CamMorelli/hshs-project-FirstStageTest/docs/teensy-4.0/dimensions_teensy40.png

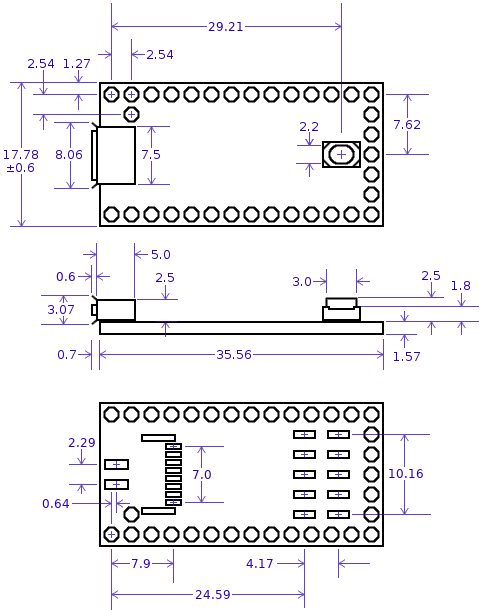
docs/teensy-4.0/dimensions_teensy40.png
