CamMorelli/hshs-project-FirstStageTest/Hardware/HSHS Interface Board 0110B/Assembly Documents/HSHS Interface Board 0110B.xlsx

Reference | Value | DESCRIPTION | Qty
C1-C4 | 1µF | CAP CER 1UF 25V X5R 0603 | 4
C5, C8 | 0.1µF |  | 2
C6, C9 | 33nF |  | 2
C7, C102, C104, C105, C202, C204, C205, C302, C304, C305, C402, C404, C405 | 10nF | CAP CER 10000PF 25V X7R 0603 | 13
C101, C201, C301, C401 | 10µF | CAP CER 10UF 16V X5R 0805 | 4
C103, C203, C303, C403 | 22µF | CAP CER 22UF 10V X7S 0805 | 4
D1-D3, D5 | LED Green | LED GREEN CLEAR 0603 SMD | 4
D4, D103, D203, D303, D403 | LED Blue | LED BLUE CLEAR 0603 SMD | 5
D101, D201, D301, D401 | LED Red | LED RED CLEAR 0603 SMD | 4
D102, D202, D302, D402 | LED Yellow | LED YELLOW CLEAR 0603 SMD | 4
H1-H4 | MountingHole |  | 4
IC1, IC2 | ACS725LLCTR-10AU-T |  | 2
J1 | Conn_01x02_Pin |  | 1
J2 | 5788801-1 | CONN D-SUB RCPT 25POS R/A SLDR | 1
J3 | 5788798-1 |  | 1
NT1 | NetTie_2 |  | 1
Q1, Q101, Q102, Q201, Q202, Q301, Q302, Q401, Q402 | SSM3K376R_A | MOSFET N-CH 30V 4A SOT23F | 9
R1, R3, R13, R105, R107, R205, R207, R305, R307, R405, R407 | 500 | RES 499 OHM 1% 1/10W 0603 | 11
R2, R4, R10, R11, R15 | 1k | -- mixed values -- | 5
R5, R102, R202, R302, R402 | 25k | -- mixed values -- | 5
R6-R9, R12, R104, R106, R204, R206, R304, R306, R404, R406 | 10k | RES 10K OHM 1% 1/10W 0603 | 13
R14 | 0.1 | RES 0.1 OHM 1% 1/3W 0805 | 1
R101, R103, R201, R203, R301, R303, R401, R403 | 15k | RES 15K OHM 1% 1/10W 0603 | 8
TP1-TP4, TP101, TP201, TP301, TP401 | 5015 | SMT Test Point- Micro Miniature-1000 pc Reels | 8
U1 | Teensy4.0_28_Pins | TEENSY 4.0 (HEADERS) | 1
U101, U201, U301, U401 | TPSM82902SISR | 3-V TO 17-V, 2-A HIGH EFFICIENCY | 4
VR101, VR201, VR301, VR401 | SM-42X104 | TRIMMER 100K OHM 0.25W GW TOP | 4
