CamMorelli/hshs-project-FirstStageTest/Hardware/HSHS Interface Board/Assembly Documents/HSHS Interface Board Symbol Table B.xlsx

Reference | Value | DESCRIPTION | Qty
C1-C5, C7 | 1¬µF | CAP CER 1UF 25V X5R 0603 | 6
C6, C9-C11, C14-C16, C19-C21, C24-C26 | 10nF | CAP CER 10000PF 25V X7R 0603 | 13
C8, C13, C18, C23 | 10¬µF | CAP CER 10UF 16V X5R 0805 | 4
C12, C17, C22, C27 | 22¬µF | CAP CER 22UF 10V X7S 0805 | 4
D1-D4 | LED Green | LED GREEN CLEAR 0603 SMD | 4
D5, D7, D10, D13, D16 | LED Blue | LED BLUE CLEAR 0603 SMD | 5
D6, D9, D12, D15 | LED Yellow | LED YELLOW CLEAR 0603 SMD | 4
D8, D11, D14, D17 | LED Red | LED RED CLEAR 0603 SMD | 4
J1 | Conn_01x02_Pin |  | 1
J2 | 2301845-2 | CONN D-SUB RCPT 15POS R/A SLDR | 1
J3 | 5788801-1 | CONN D-SUB RCPT 25POS R/A SLDR | 1
NT1 | NetTie_2 |  | 1
Q1-Q9 | SSM3K376R_A | MOSFET N-CH 30V 4A SOT23F | 9
R1, R3, R5, R7, R8, R10, R17, R18, R30, R31, R43, R44, R56, R57 | 500 | RES 499 OHM 1% 1/10W 0603 | 14
R2, R6 | 1k | RES 1K OHM 1% 1/10W 0603 | 2
R4, R9, R11-R15, R19-R22, R26, R27, R32-R35, R39, R40, R45-R48, R52, R53, R58-R61, R65, R66 | 10k | RES 10K OHM 1% 1/10W 0603 | 31
R16, R23, R24, R36, R37, R49, R50, R62, R63 | 0.1 | RES 0.1 OHM 1% 1/3W 0805 | 9
R25, R29, R38, R42, R51, R55, R64, R68 | 15k | RES 15K OHM 1% 1/10W 0603 | 8
R28, R41, R54, R67 | 25k | RES SMD 24.9K OHM 1% 1/10W 0603 | 4
TP1-TP13 | 5015 | SMT Test Point- Micro Miniature-1000 pc Reels | 13
U1 | Teensy4.0_28_Pins | TEENSY 4.0 (HEADERS) | 1
U2-U5 | TPSM82902SISR | 3-V TO 17-V, 2-A HIGH EFFICIENCY | 4
VR1-VR4 | SM-42X104 | TRIMMER 100K OHM 0.25W GW TOP | 4
