CamMorelli/hshs-project-FirstStageTest/docs/Off Board Components/Lasers/Nichia NDG7475.pdf

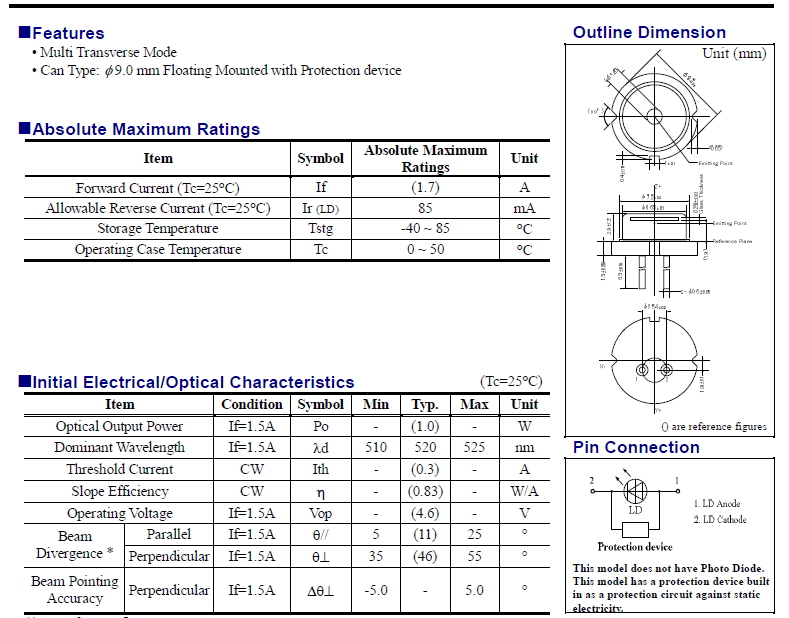
[picture p5: figure]
