CamMorelli/hshs-project-FirstStageTest/Hardware/HSHS Test Board 0111/HSHS Test Board 0111.csv

Reference | Value | Footprint | Datasheet | AVAILABILITY | Arrow Part Number | Arrow Price/Stock | DESCRIPTION | Digikey Price Stock | Digikey_Part_Number | Height | MF | MP | Manufacturer Part Number | Manufacturer_Name | Mouser Part Number | Mouser Price/Stock | PACKAGE | PRICE | PURCHASE-URL | Qty
J1 | DB25_Receptacle | Global_Footprint_Library:57888011_A | https://www.te.com/commerce/DocumentDelivery/DDEController?Action=showdoc |  | 5788801-1 | https://www.arrow.com/en/products/5788801-1/te-connectivity?region=nac | CONN D-SUB RCPT 25POS R/A SLDR | https://www.digikey.com/en/products/detail/te-connectivity-amp-connectors/5788801-1/1279852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 | A35139-ND | 12.93 |  |  | 5788801-1 | TE Connectivity | 571-5788801-1 | https://www.mouser.co.uk/ProductDetail/TE-Connectivity-AMP/5788801-1?qs=PmjM%2FwY1RToSHOZP%252ByStZg%3D%3D |  | 8.04 |  | 1
J2 | DB25_Plug | Global_Footprint_Library:5788794_1 Mod From 57888011_A | https://www.te.com/commerce/DocumentDelivery/DDEController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 |  |  |  | CONN D-SUB PLUG 25POS R/A SLDR | https://www.digikey.com/en/products/detail/te-connectivity-amp-connectors/5788794-1/1279845 | A35132-ND |  |  |  | 5788794-1 | TE Connectivity |  |  |  |  |  | 1
R1-R8 | 0.1 | Resistor_SMD:R_0805_2012Metric | ~ |  |  |  |  |  |  |  |  |  |  |  |  |  |  |  |  | 8
TP1-TP8 | 5015 | Global_Footprint_Library:KEYSTONE_5015 | https://www.keyelco.com/userAssets/file/M65p55.pdf | In Stock |  |  | SMT Test Point- Micro Miniature-1000 pc Reels | https://www.digikey.com/en/products/detail/keystone-electronics/5015/278885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 | 36-5015CT-ND |  | Keystone Electronics | 5015 | 5015 | Keystone Electronics |  |  | None | 0.3684 | https://pricing.snapeda.com/search/part/5015/?ref=eda | 8
