CamMorelli/hshs-project-FirstStageTest/Hardware/HSHS Test Board 0111/Assembly Docs/HSHS Test Board 0111.xlsx

Reference | Value | Qty
J1 | DB25_Receptacle | 1
J2 | DB25_Plug | 1
R1-R8 | 0.1 | 8
TP1-TP8 | 5015 | 8
