CamMorelli/hshs-project-FirstStageTest/Hardware/HSHS Interface Board 0110A/Assembly Documents/Screen Shot 2024-03-24 at 6.15.10 PM.png

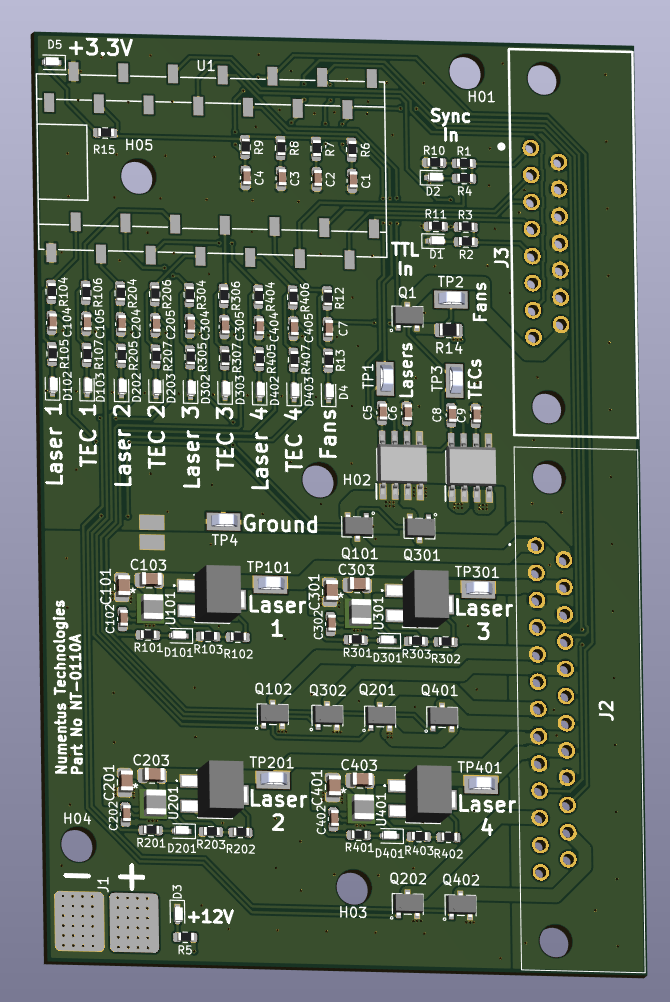
Hardware/HSHS Interface Board 0110A/Assembly Documents/Screen Shot 2024-03-24 at 6.15.10 PM.png
