CamMorelli/hshs-project-FirstStageTest/Hardware/HSHS Interface Board 0110B/Assembly Documents/Screen Shot 2024-04-10 at 11.27.31 AM.png

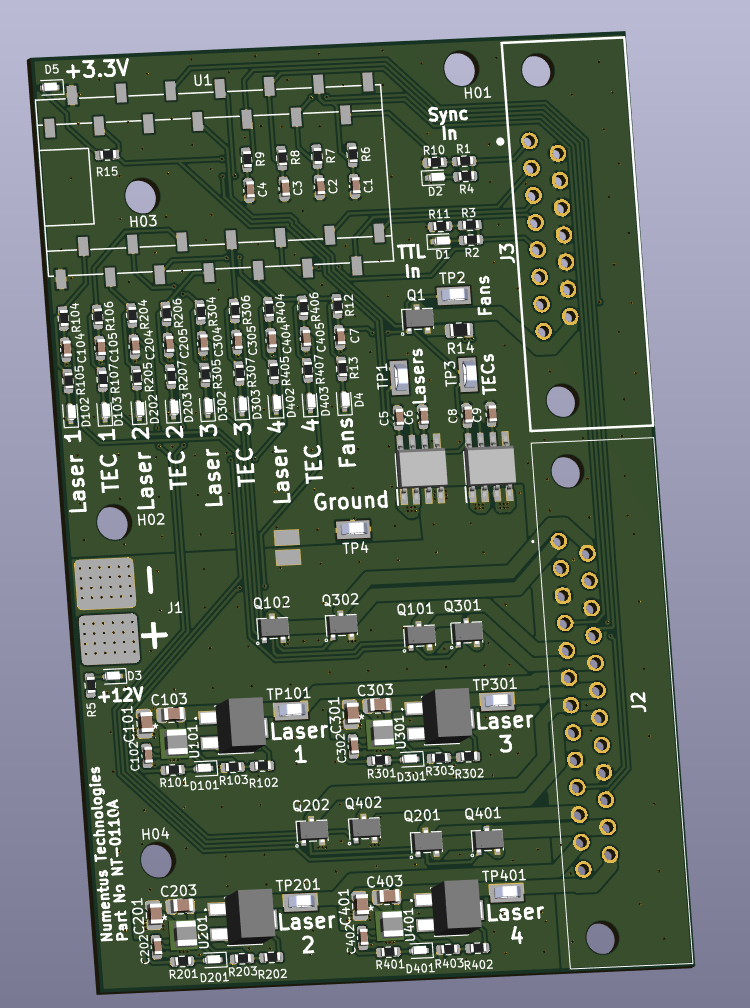
Hardware/HSHS Interface Board 0110B/Assembly Documents/Screen Shot 2024-04-10 at 11.27.31 AM.png
