CamMorelli/hshs-project-FirstStageTest/Hardware/HSHS Interface Board 1010C/Assembly Documents/Screen Shot 2024-04-26 at 10.37.50 AM.png

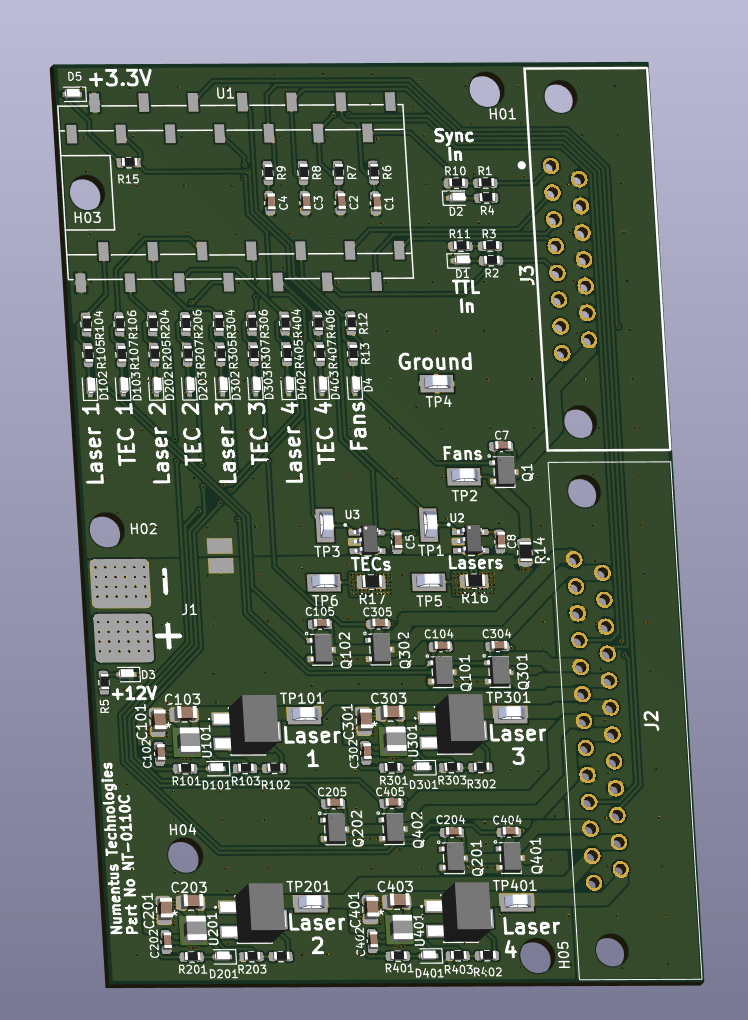
Hardware/HSHS Interface Board 1010C/Assembly Documents/Screen Shot 2024-04-26 at 10.37.50 AM.png
