CamMorelli/hshs-project-FirstStageTest/Hardware/HSHS Interface Board/Assembly Documents/Screen Shot 2024-03-11 at 11.47.38 AM.png

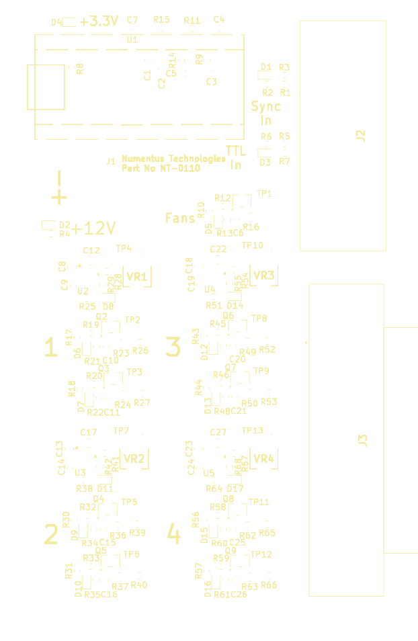
Hardware/HSHS Interface Board/Assembly Documents/Screen Shot 2024-03-11 at 11.47.38 AM.png
