CamMorelli/hshs-project-FirstStageTest/Hardware/HSHS Interface Board/Assembly Documents/Screen Shot 2024-03-11 at 12.02.20 PM.png

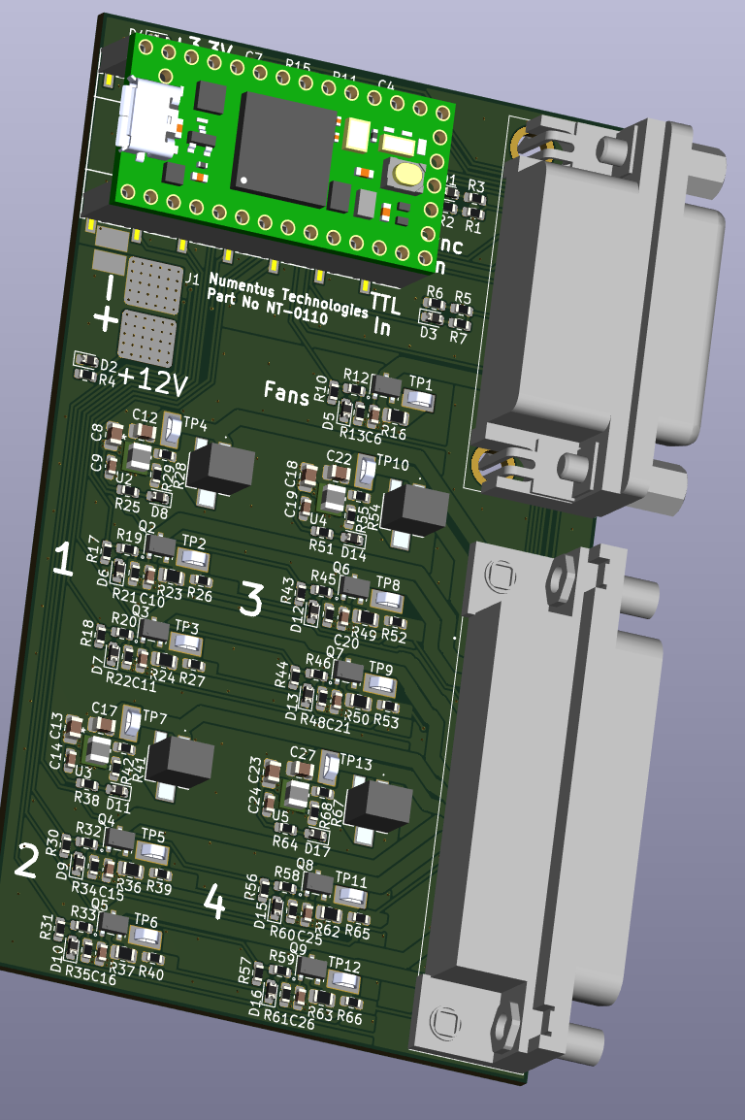
Hardware/HSHS Interface Board/Assembly Documents/Screen Shot 2024-03-11 at 12.02.20 PM.png
