CamMorelli/hshs-project-FirstStageTest/Hardware/HSHS Test Board 0111/Assembly Docs/Screen Shot 2024-04-04 at 2.46.10 PM.png

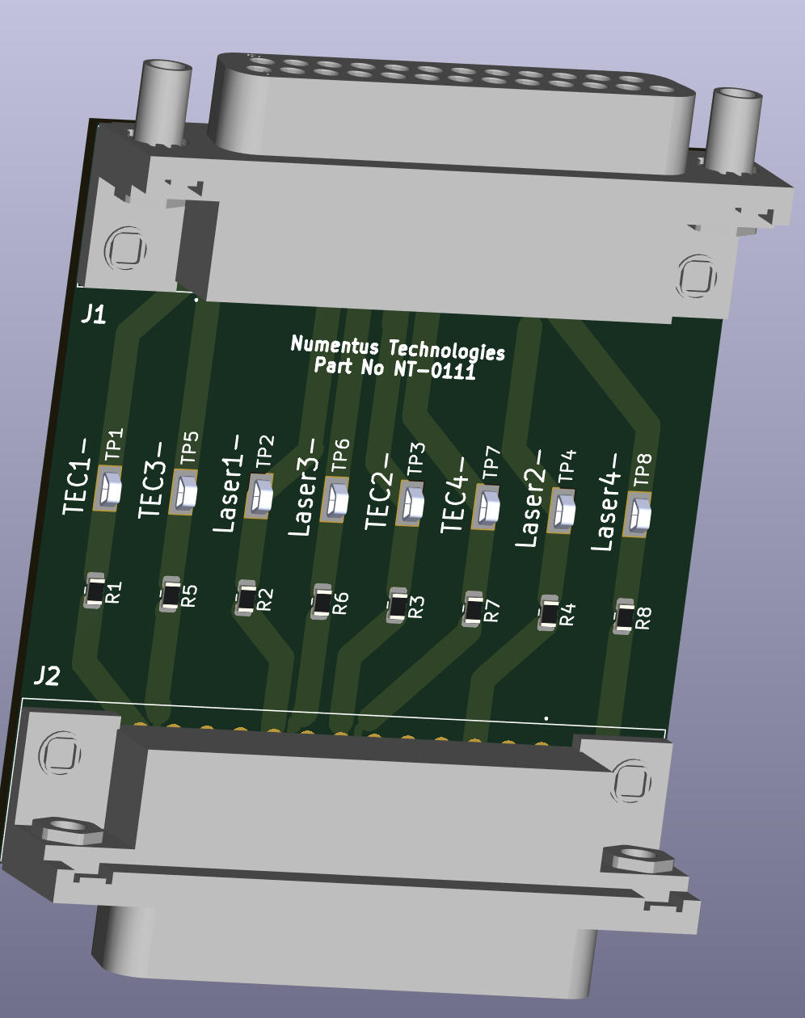
Hardware/HSHS Test Board 0111/Assembly Docs/Screen Shot 2024-04-04 at 2.46.10 PM.png
