CamMorelli/hshs-project-FirstStageTest/Hardware/HSHS Interface Board 1010C/Assembly Documents/HSHS Interface Board 1010C-F_Fab.pdf

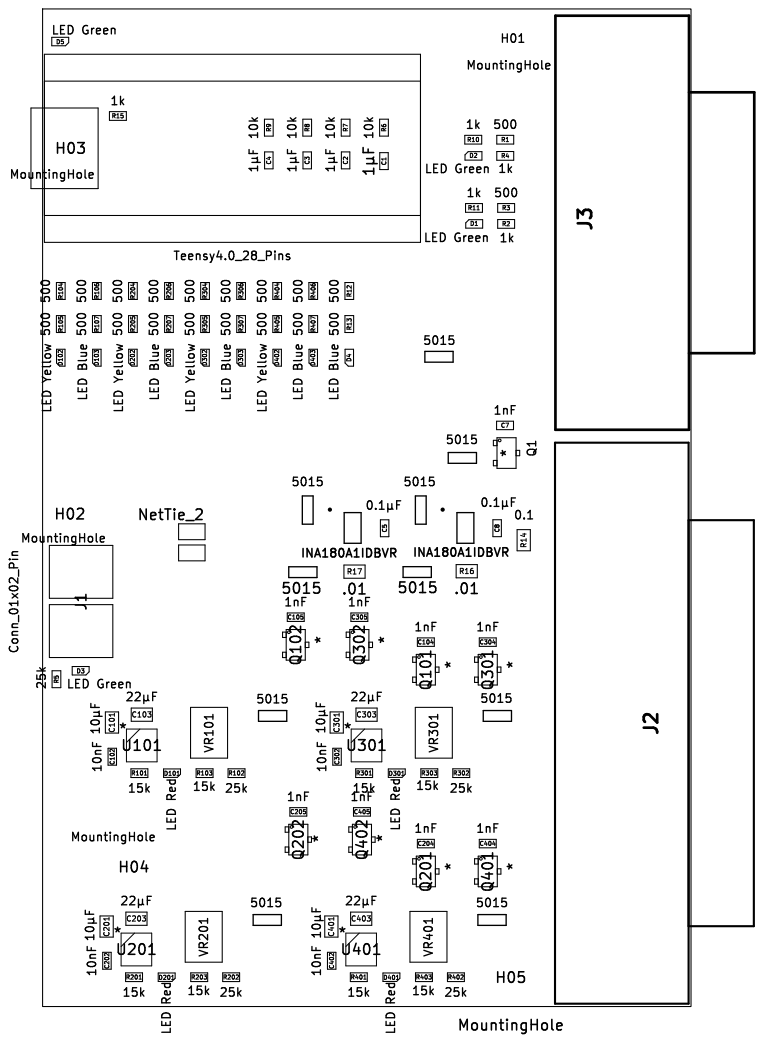
[picture p20: page 1]

* Q101 þÿ10µF C101 MountingHole H03 þÿ10µF C201 5015 MountingHole H05 10nF C402 *U201
