CamMorelli/hshs-project-FirstStageTest/Hardware/HSHS Test Board 0111/Assembly Docs/HSHS Test Board 0111-F_Silkscreen.pdf

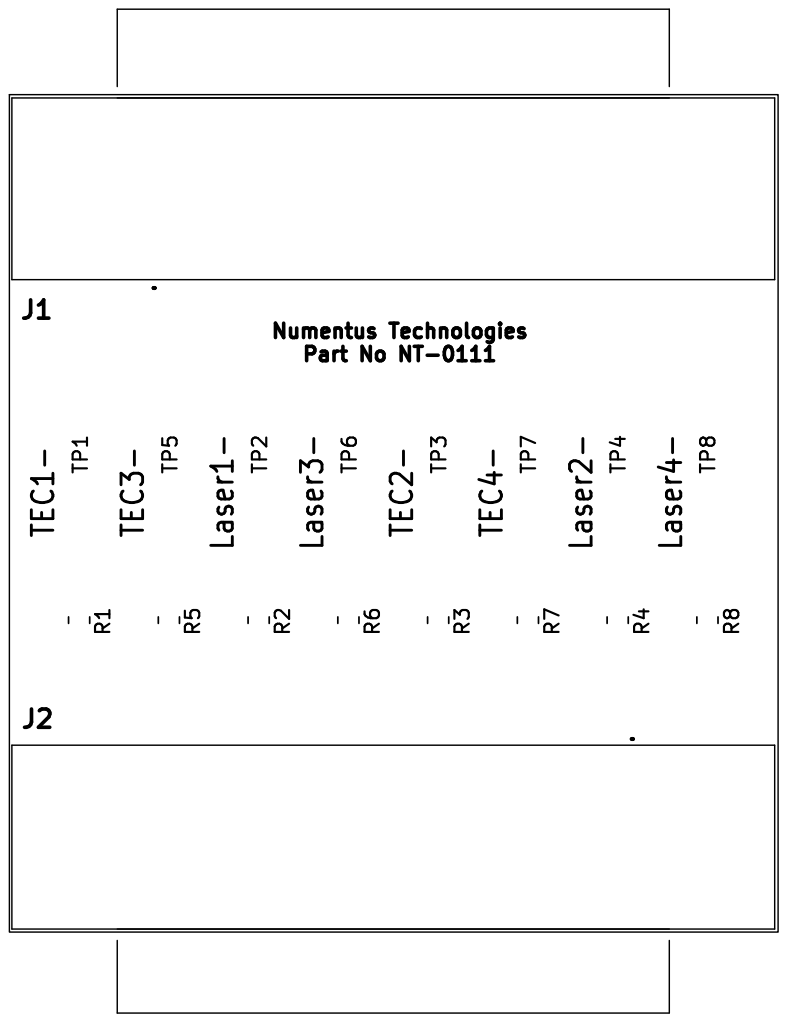
[picture p21: page 1]

TEC4- Laser1- Laser2- TEC1- TEC3- Laser3- Laser4- TEC2- Numentus Technologies Part No NT-0111 TP8 J1
