CamMorelli/hshs-project-FirstStageTest/docs/PCB Components/Connectors/ENG_CD_2301845_H.pdf

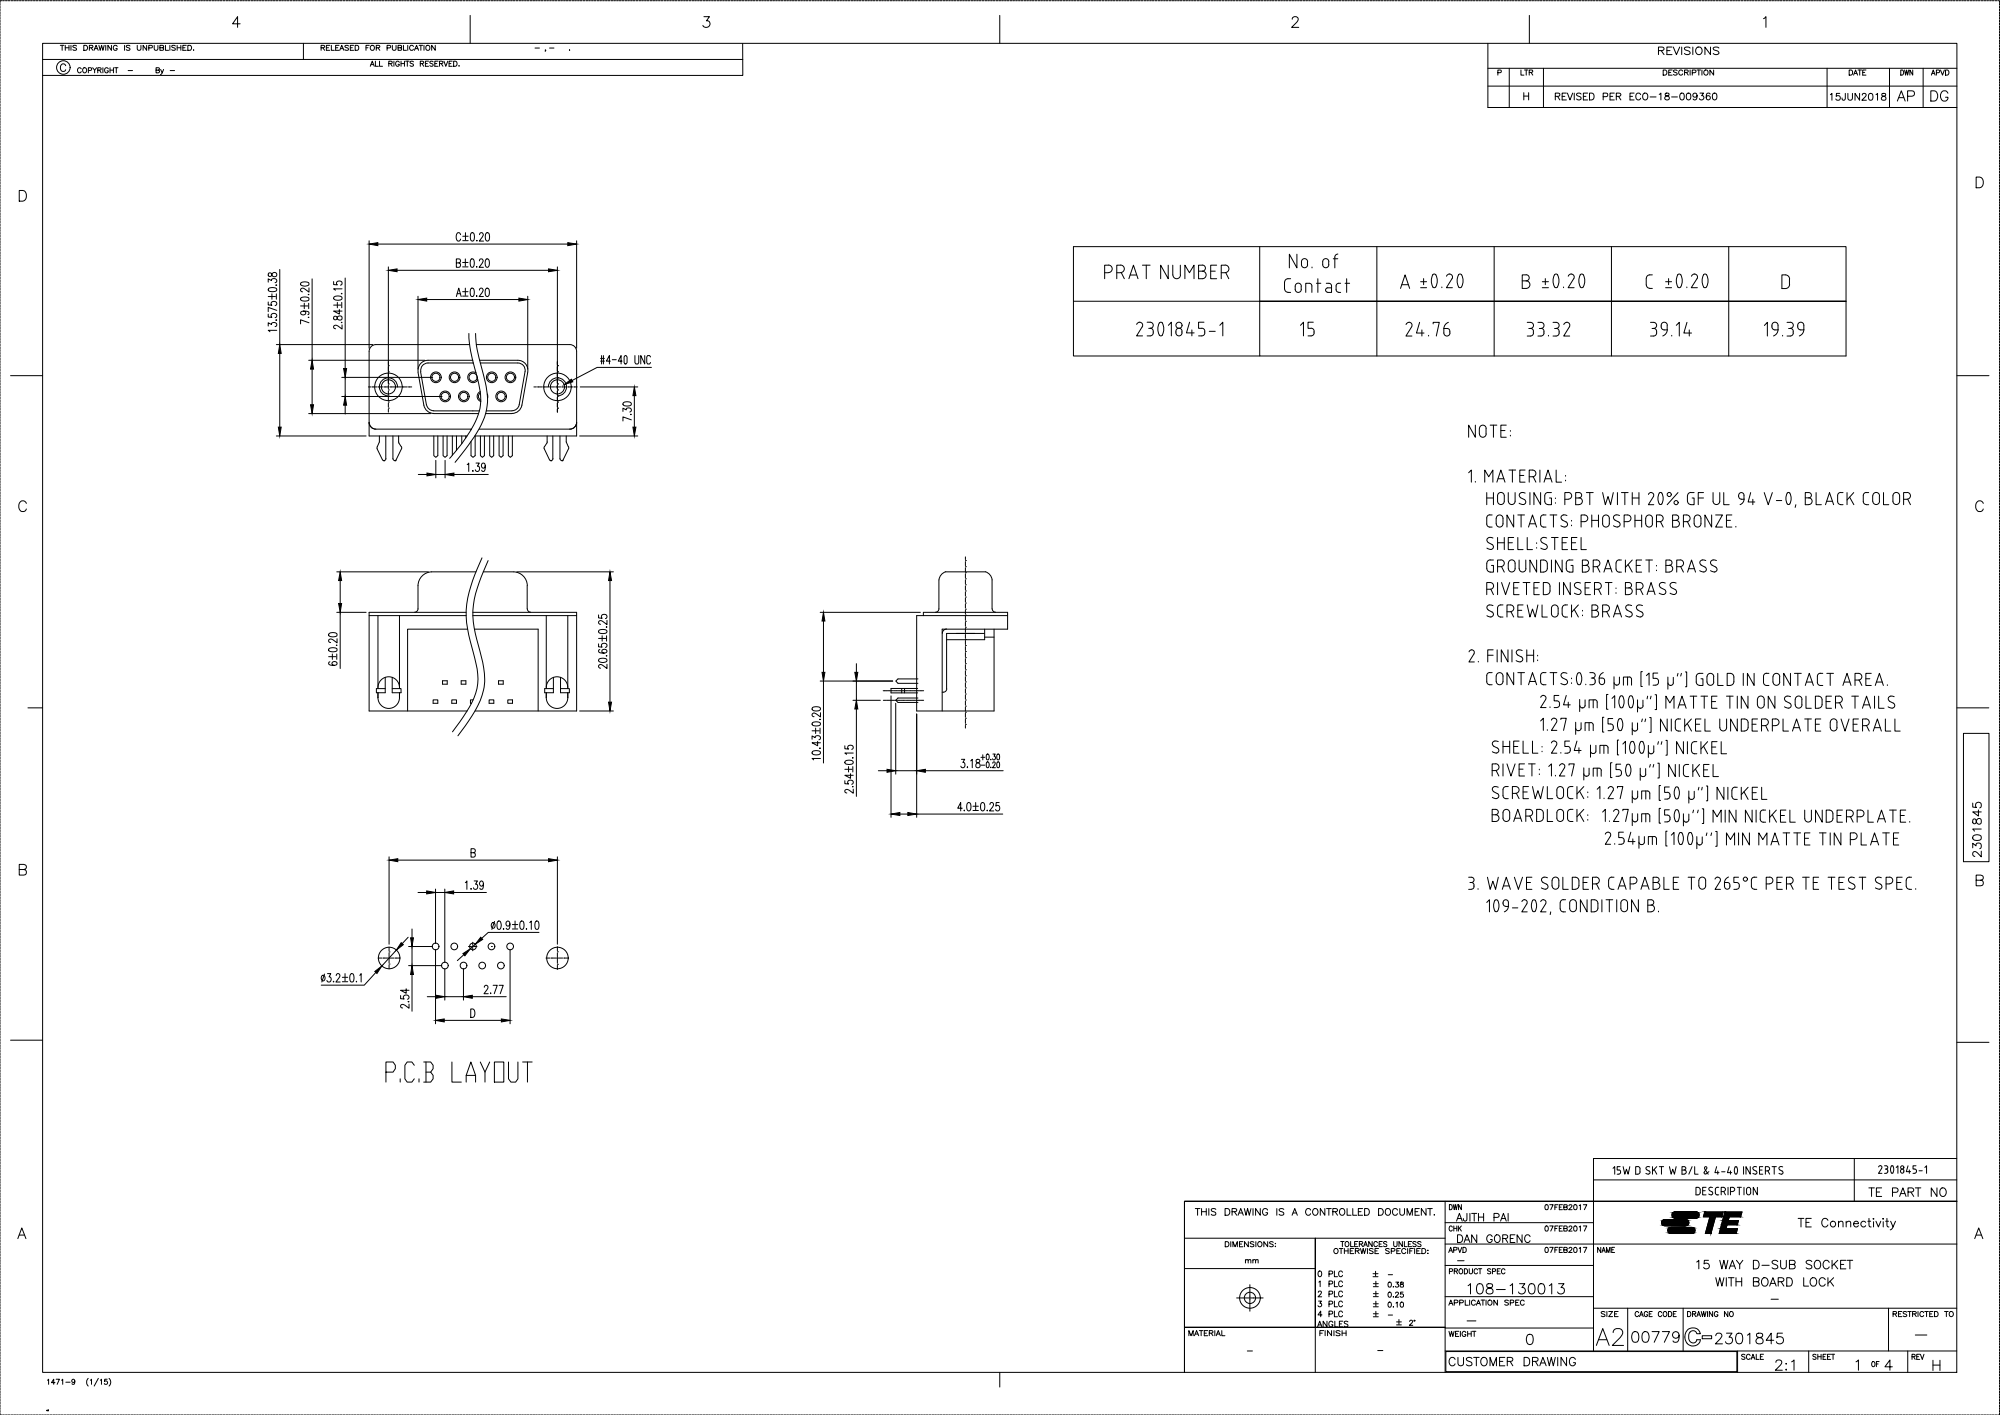
[picture p29: page 1]

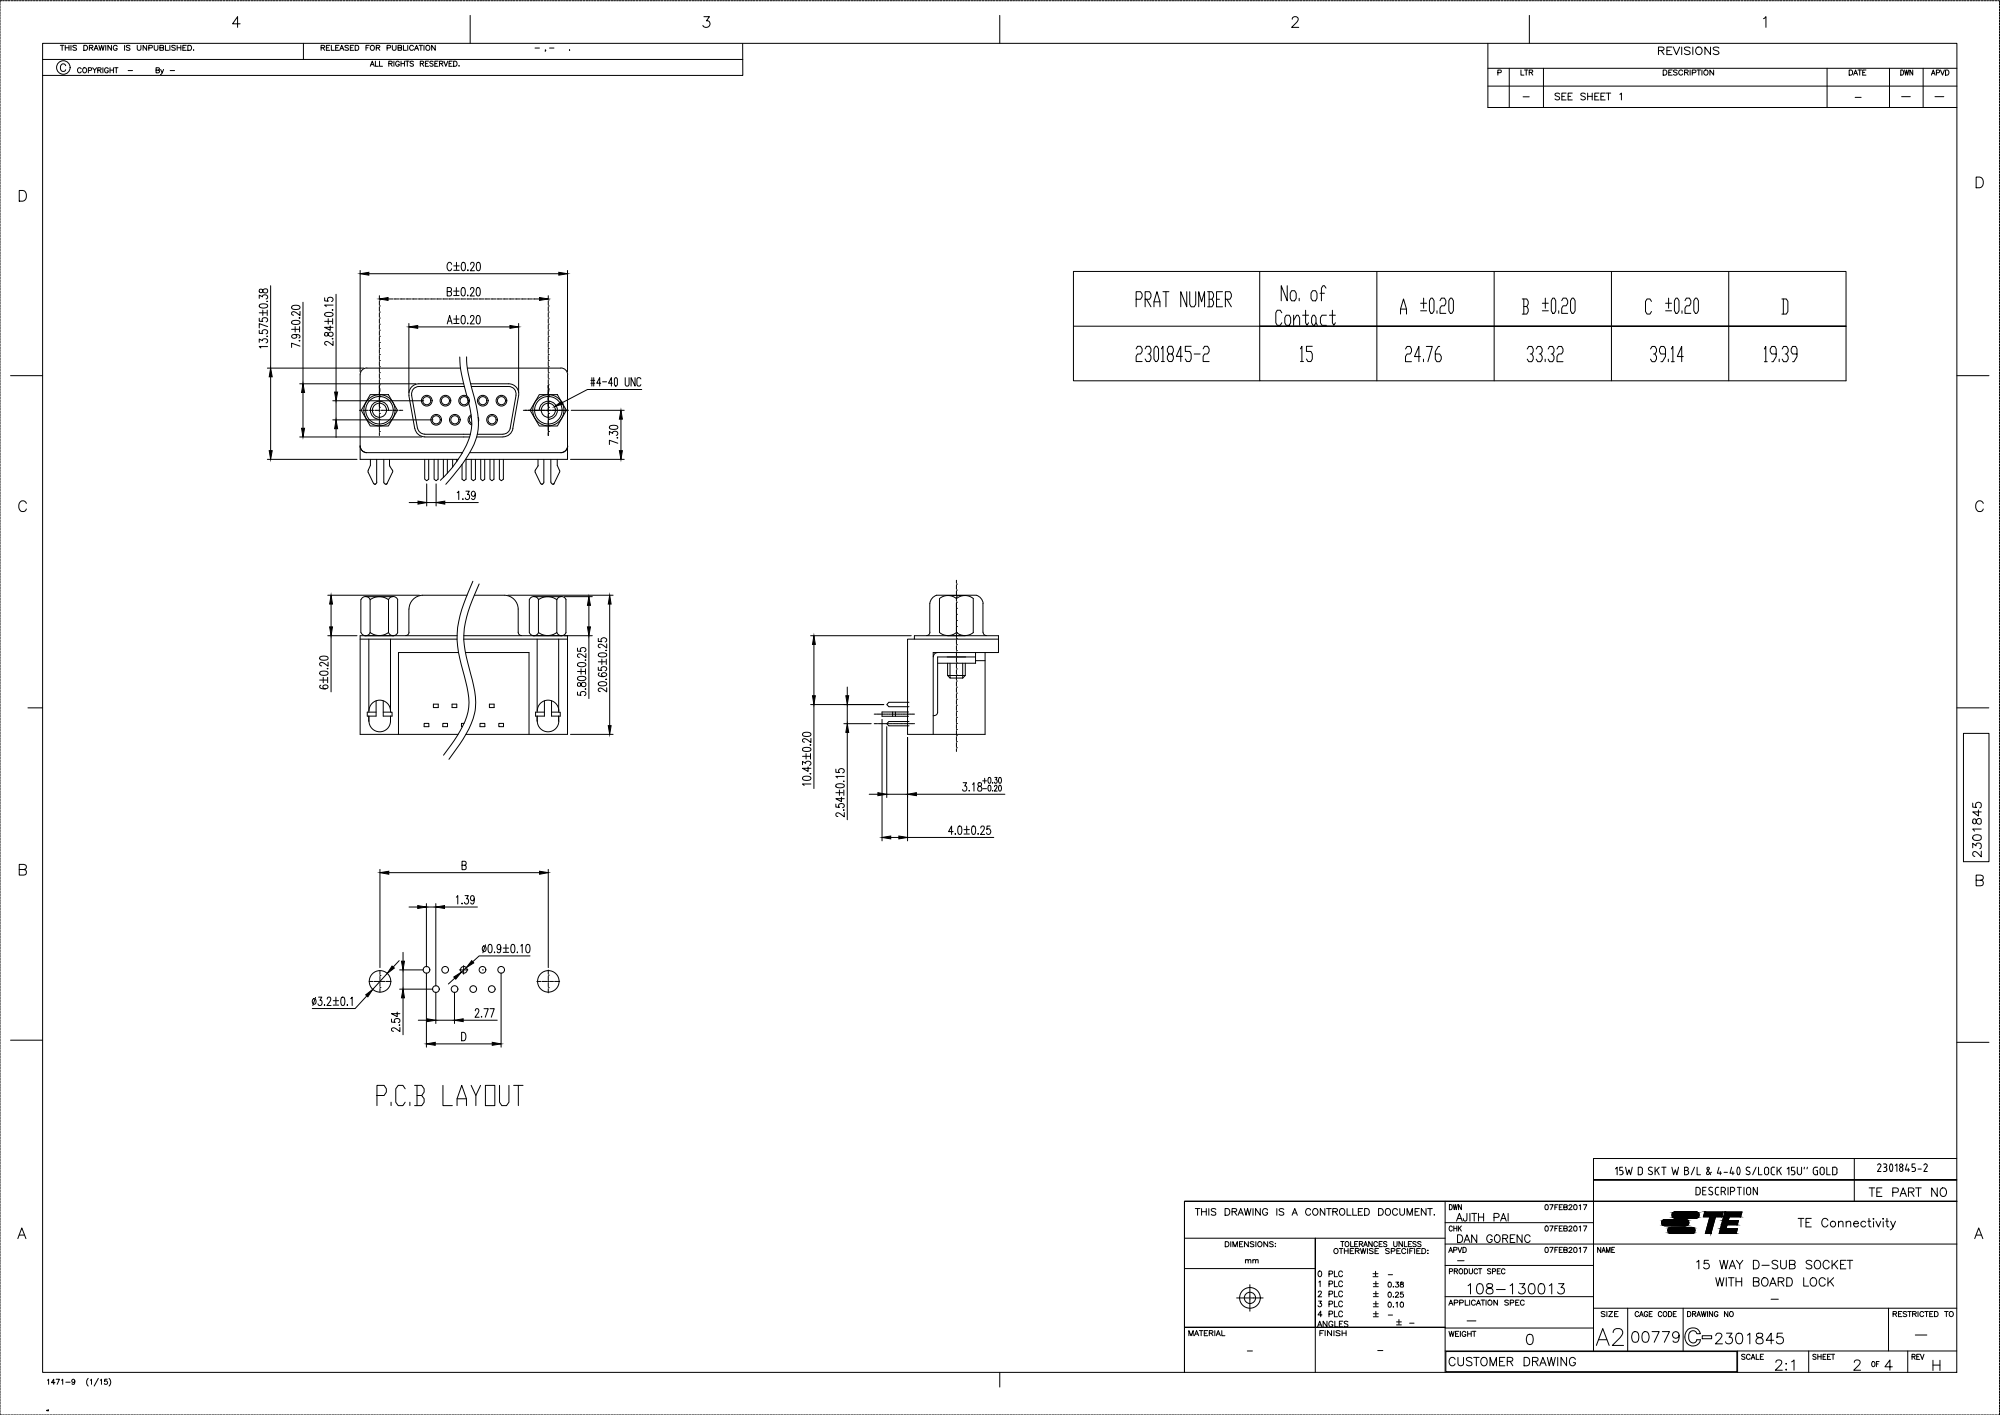
[picture p30: page 2]

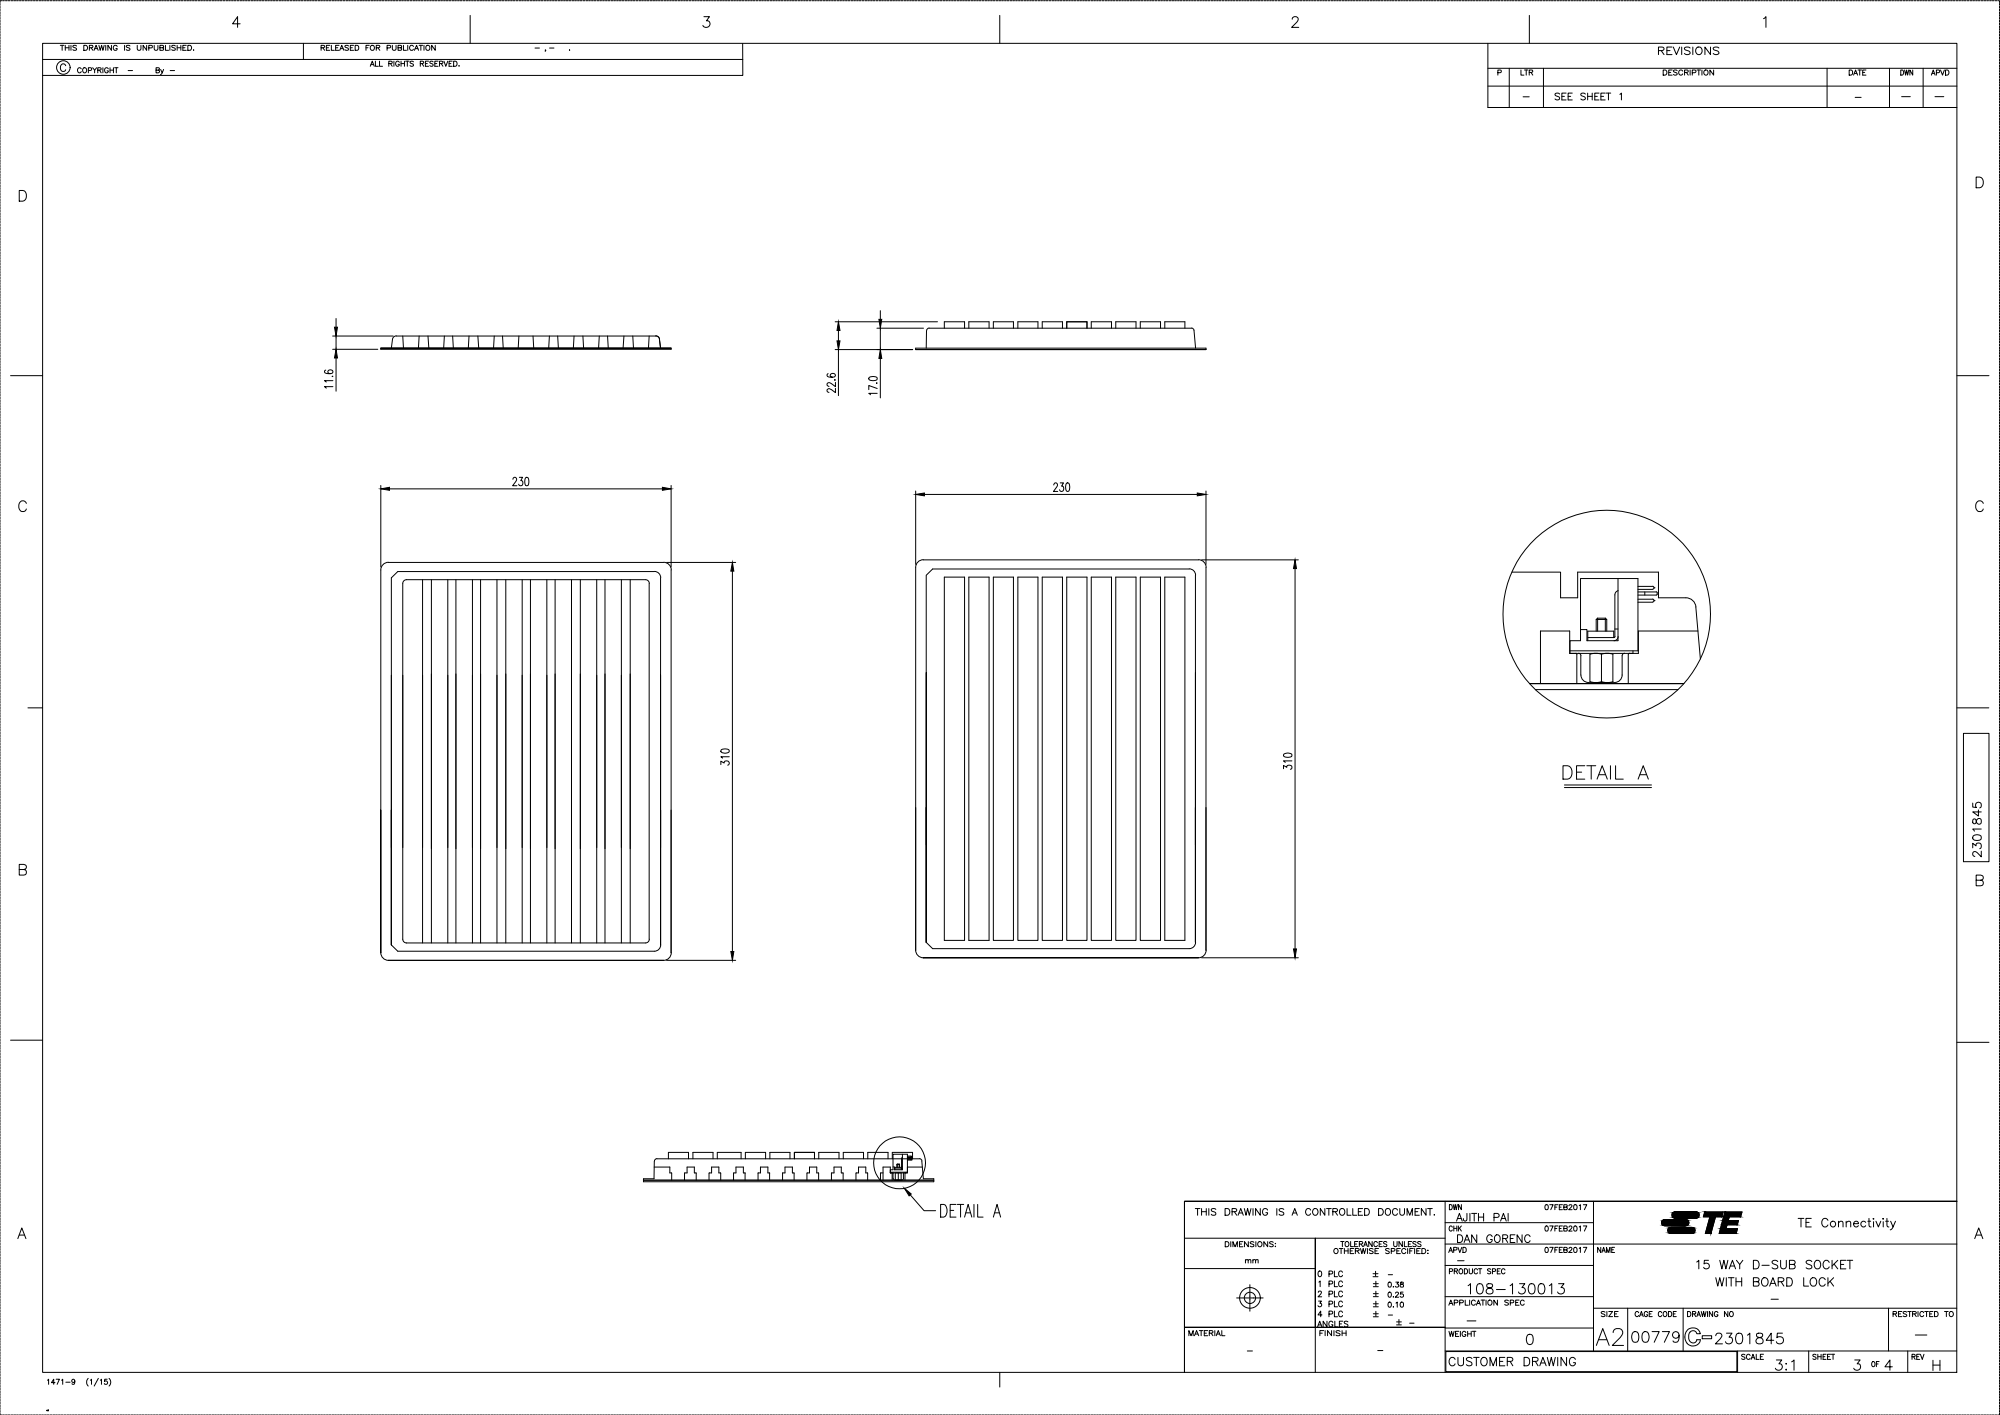
[picture p31: page 3]

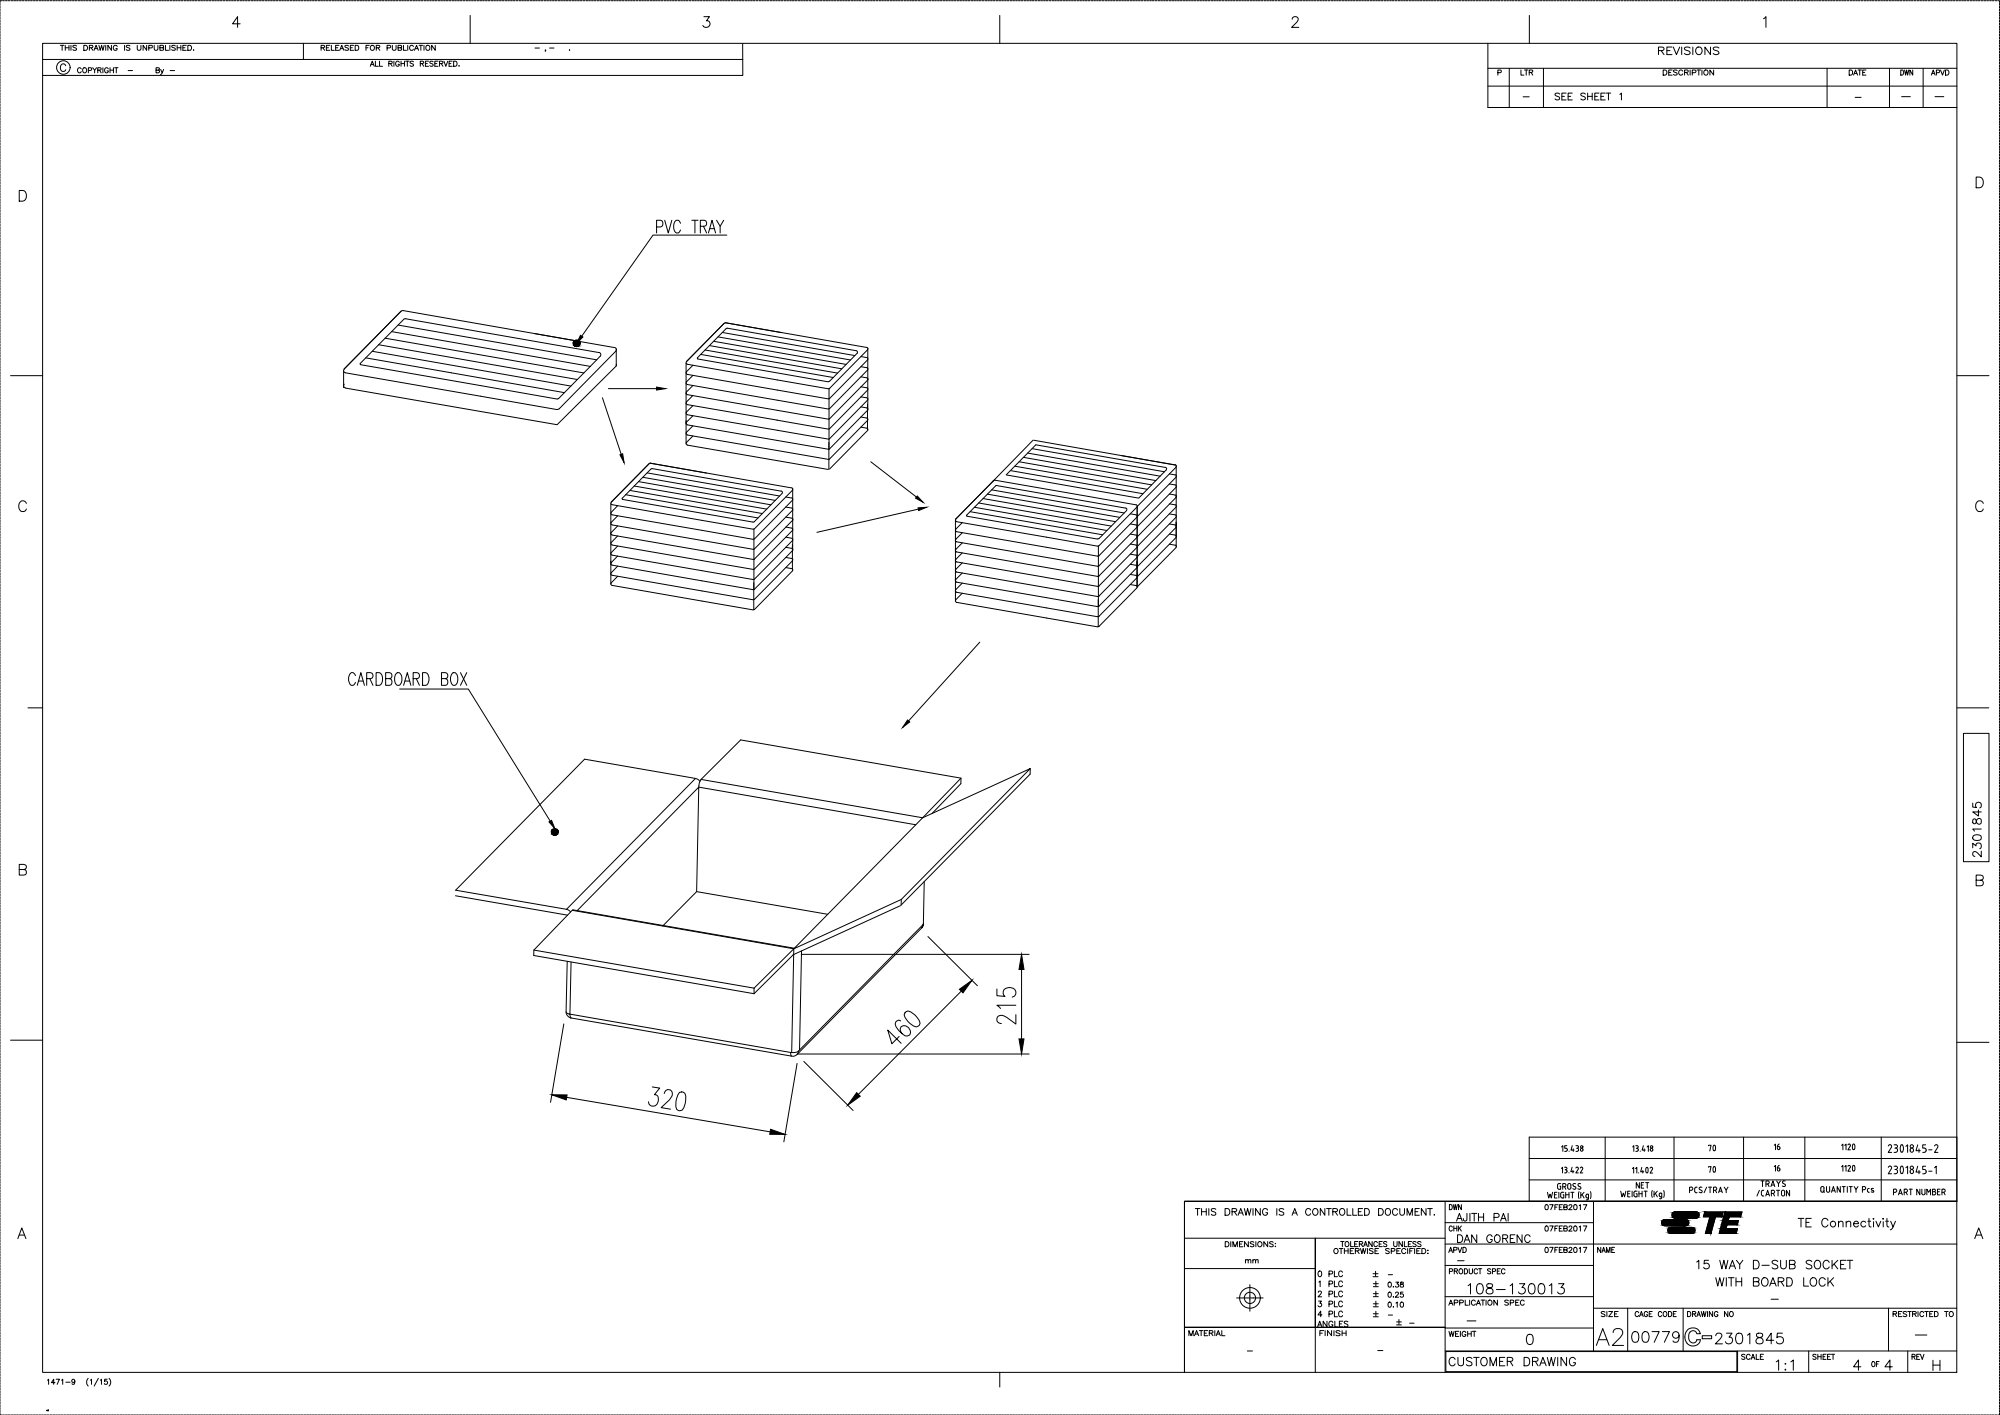
[picture p32: page 4]
