CamMorelli/hshs-project-FirstStageTest/docs/PCB Components/Connectors/ENG_CD_5788798_A1.pdf

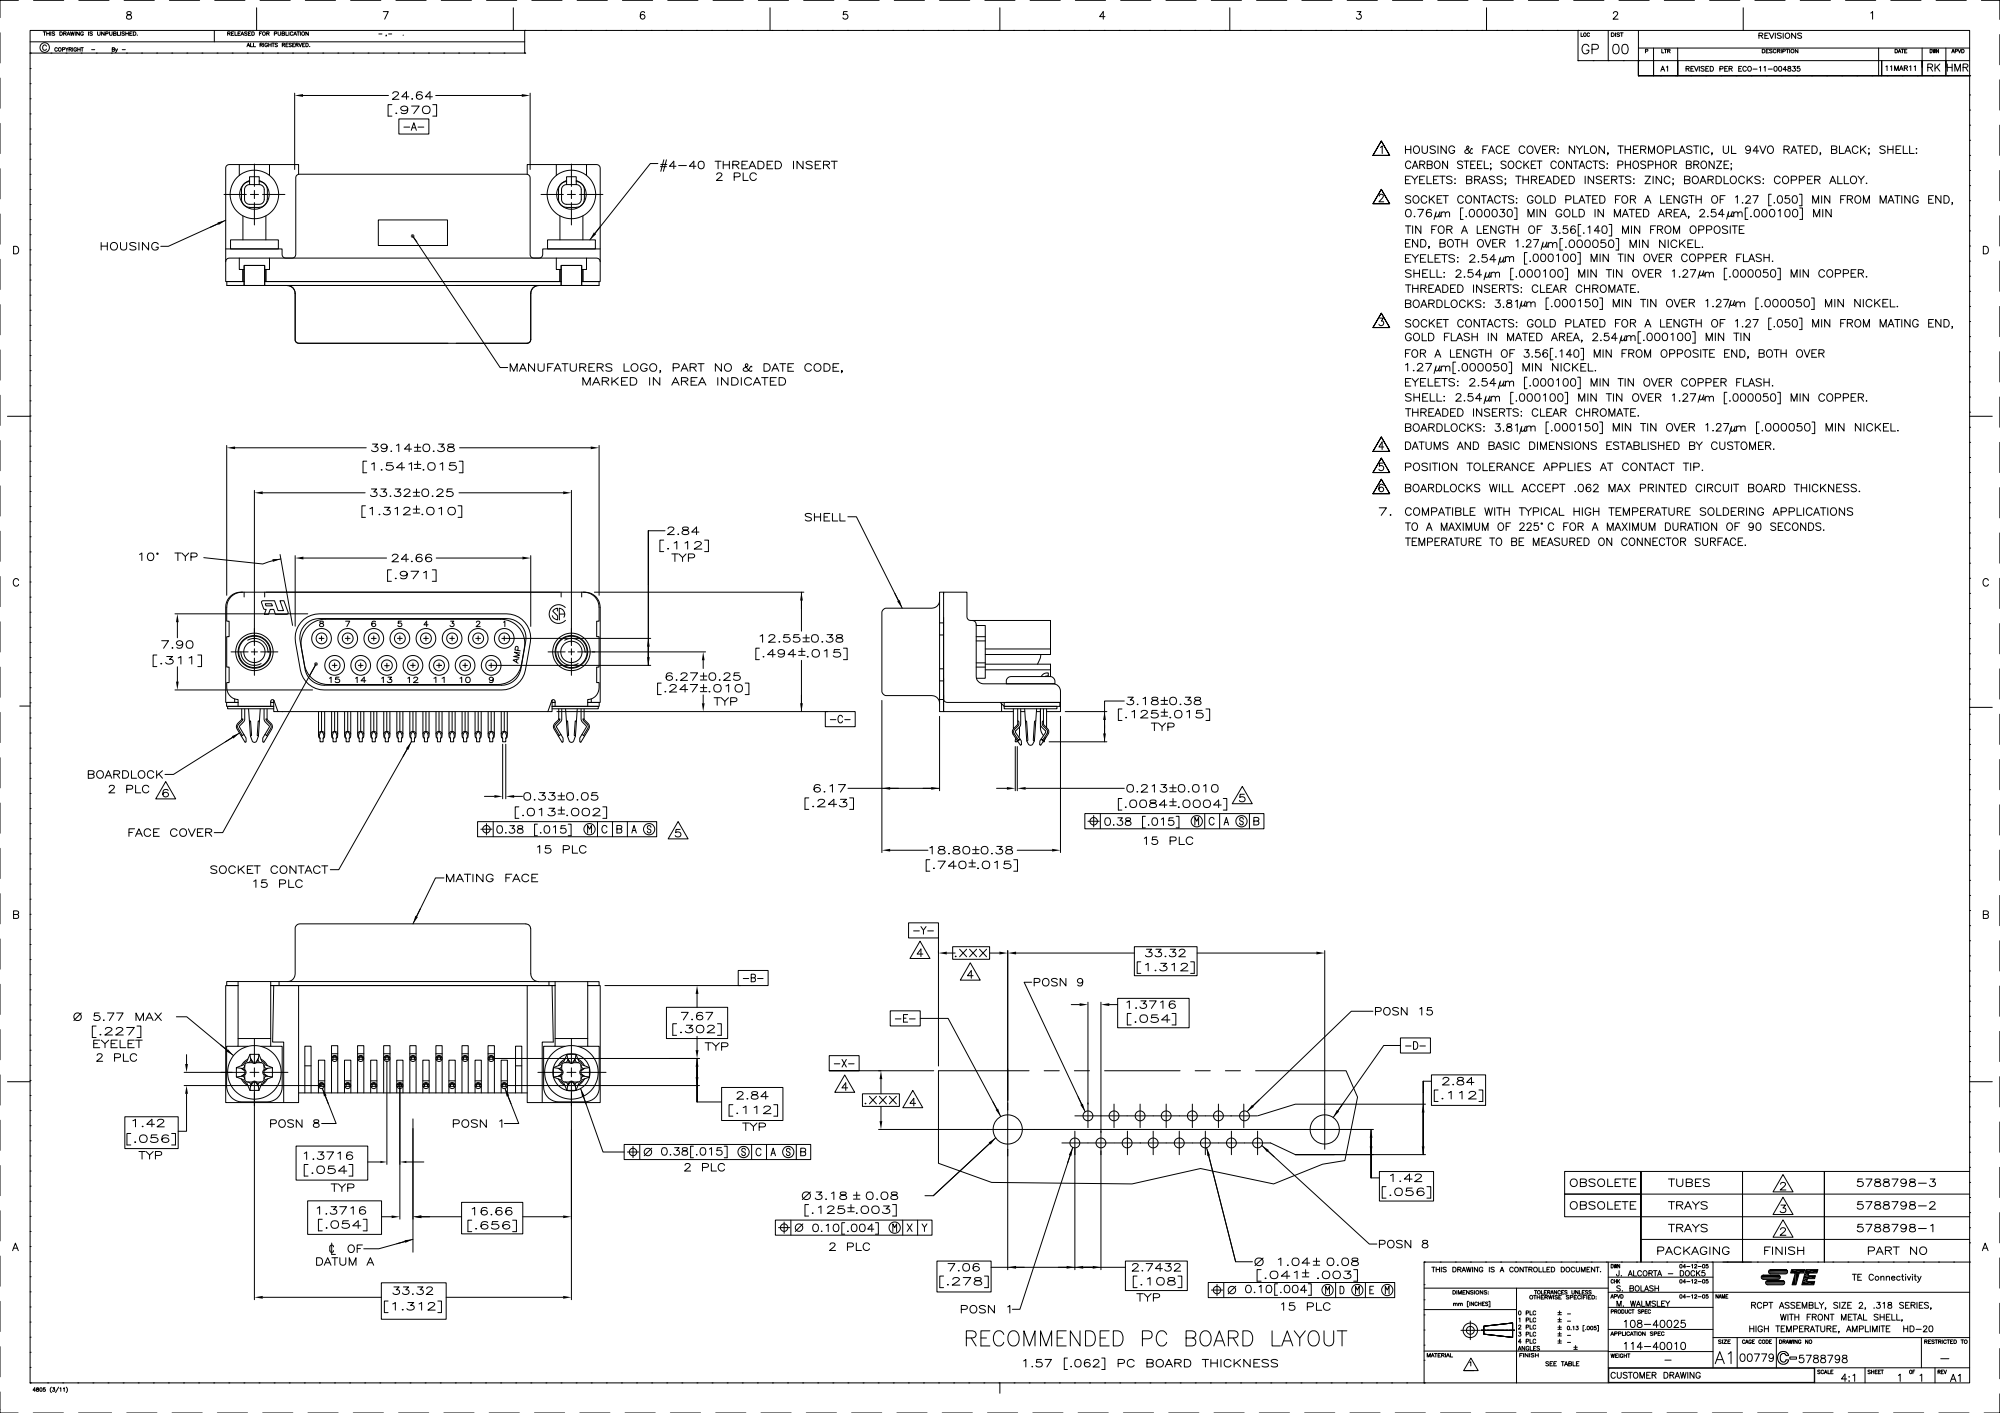
[picture p33: page 1]
