CamMorelli/hshs-project-FirstStageTest/docs/PCB Components/Connectors/ENG_CD_5788801_O.pdf

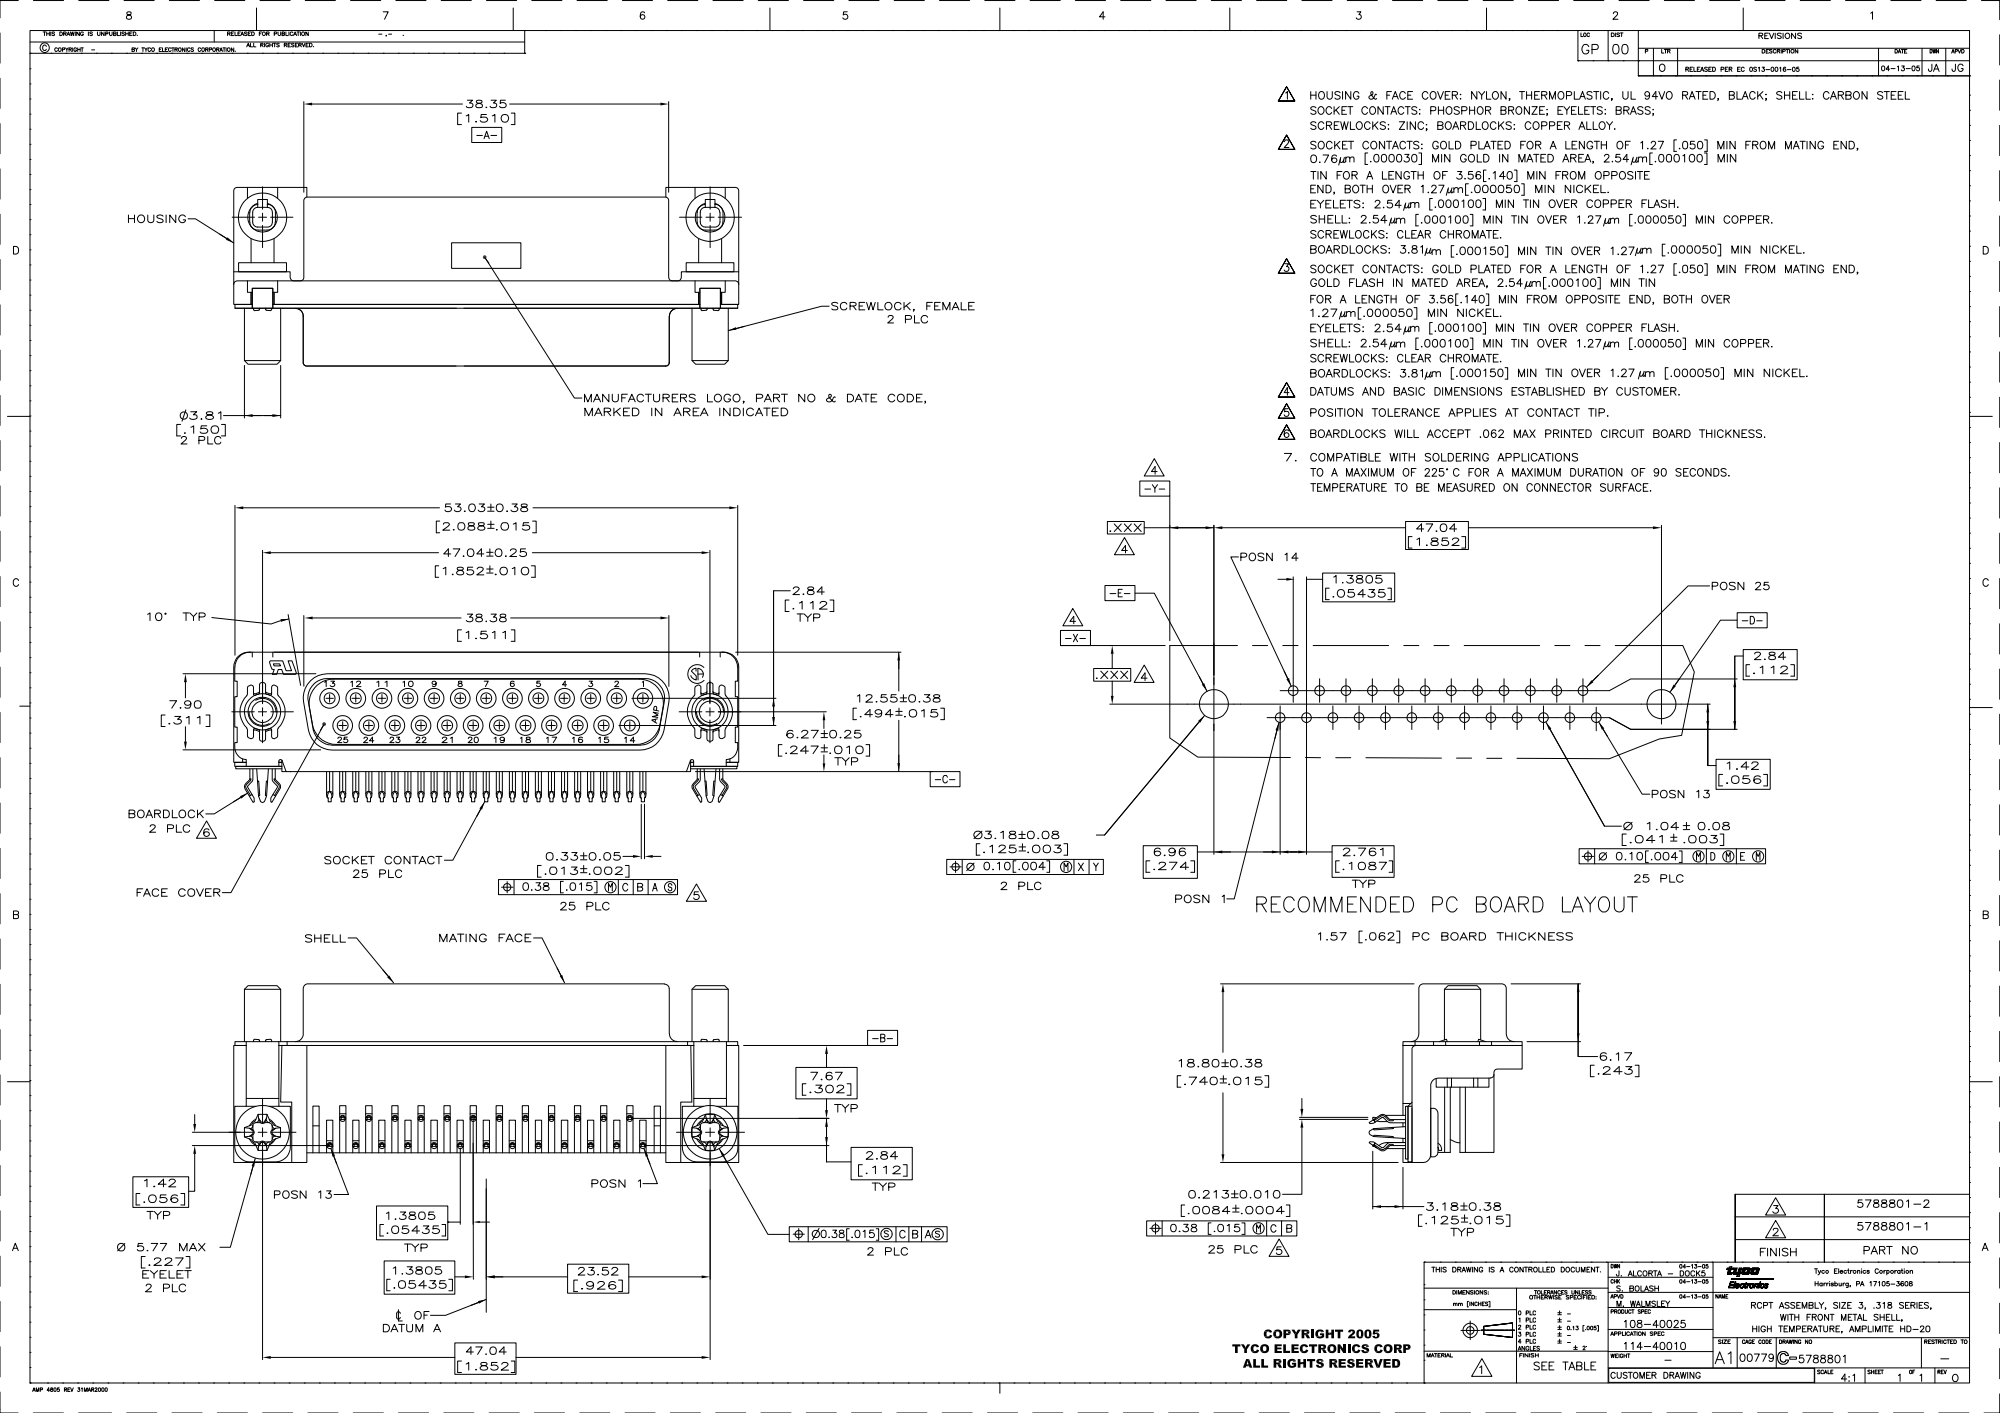
[picture p34: page 1]
