CamMorelli/hshs-project-FirstStageTest/Hardware/HSHS Interface Board 0110A/Assembly Documents/HSHS Interface Board 0110A-F_Fab Crop.pdf

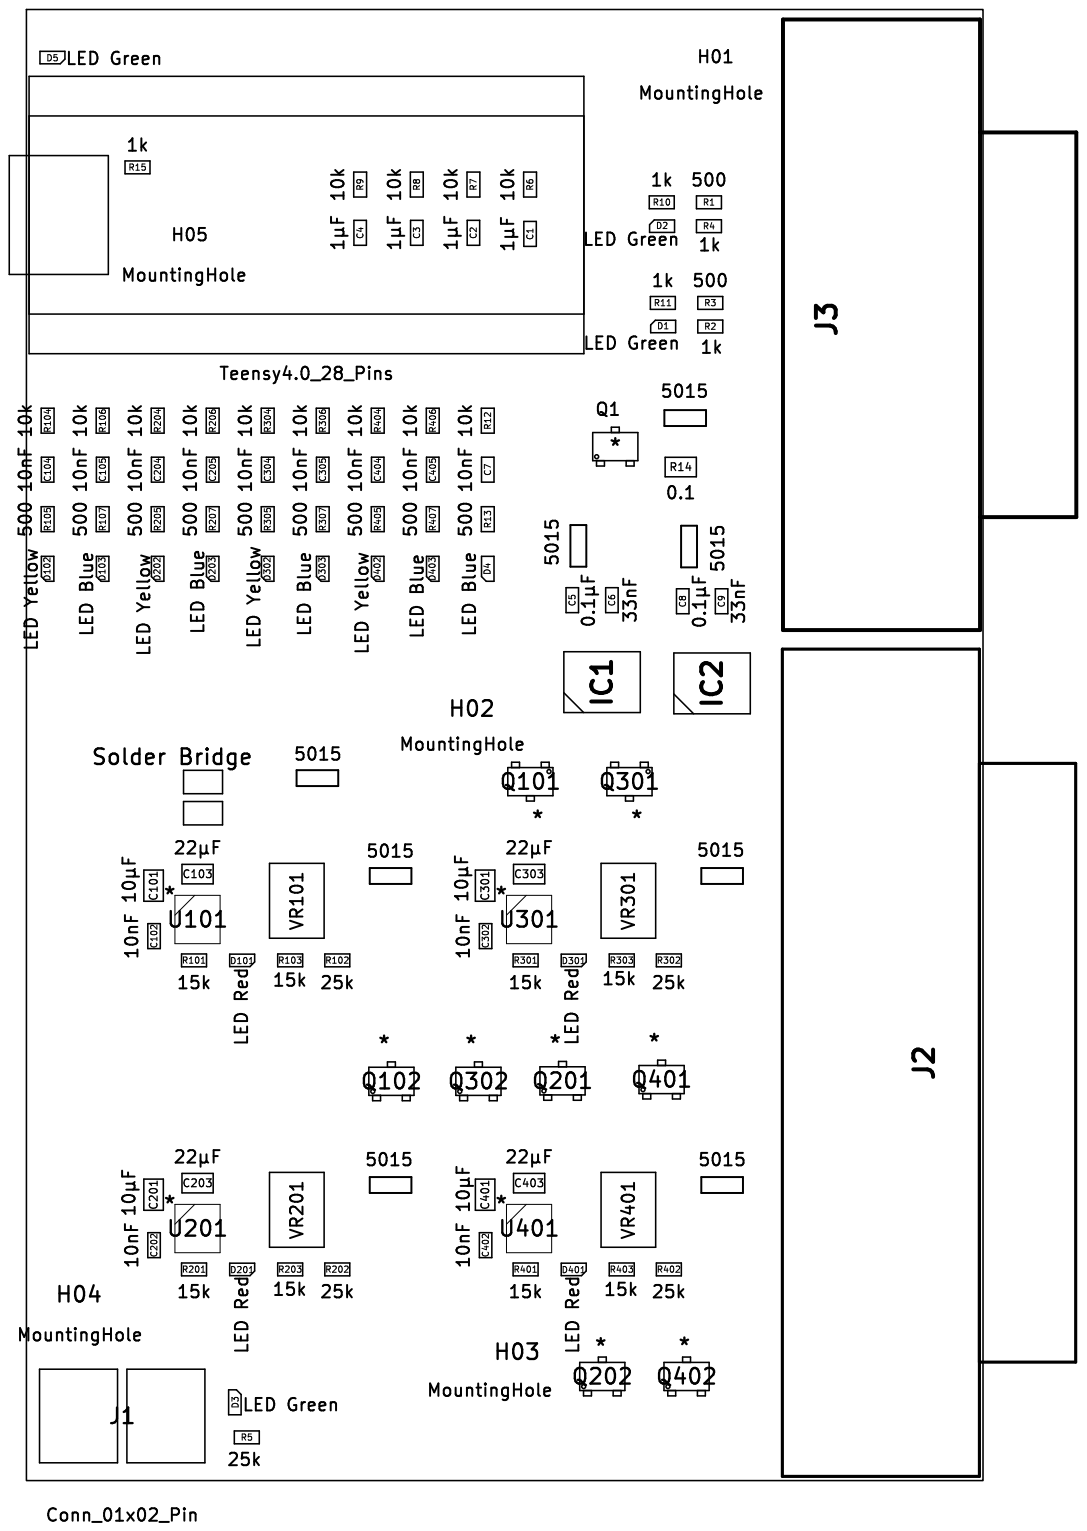
[picture p35: page 1]
