CamMorelli/hshs-project-FirstStageTest/Hardware/HSHS Interface Board 0110A/Assembly Documents/HSHS Interface Board 0110A-F_Silkscreen Crop.pdf

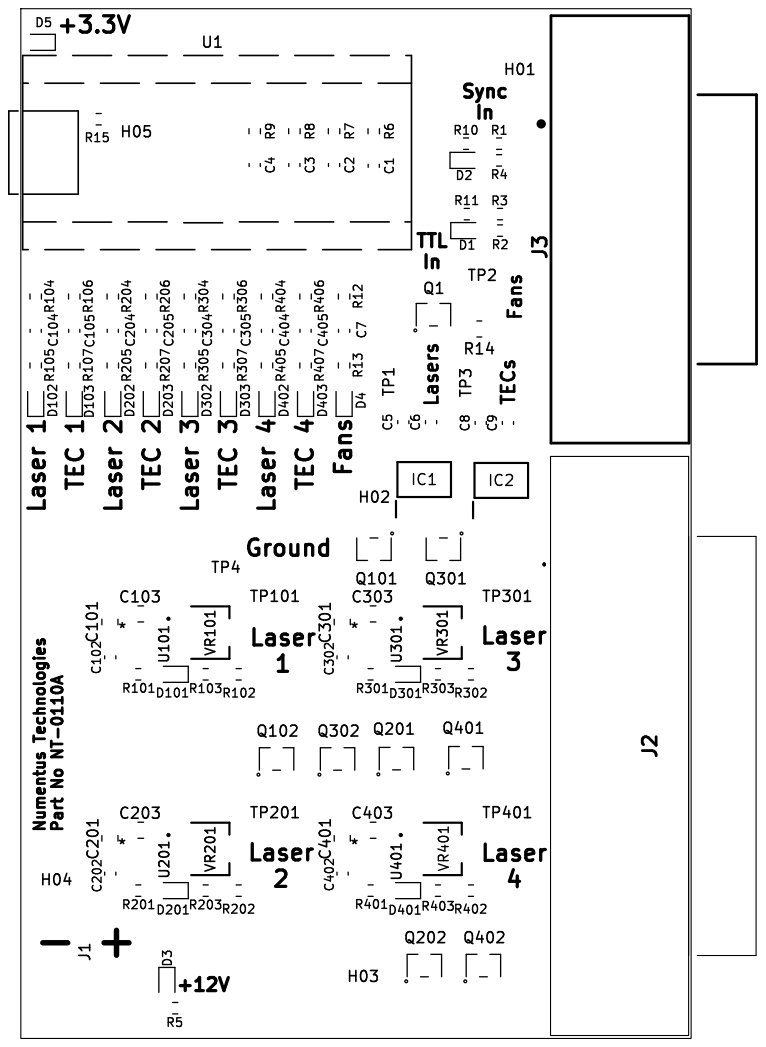
[picture p36: page 1]
