CamMorelli/hshs-project-FirstStageTest/Hardware/HSHS Interface Board 0110B/Assembly Documents/HSHS Interface Board 0110B-B_Cu.pdf

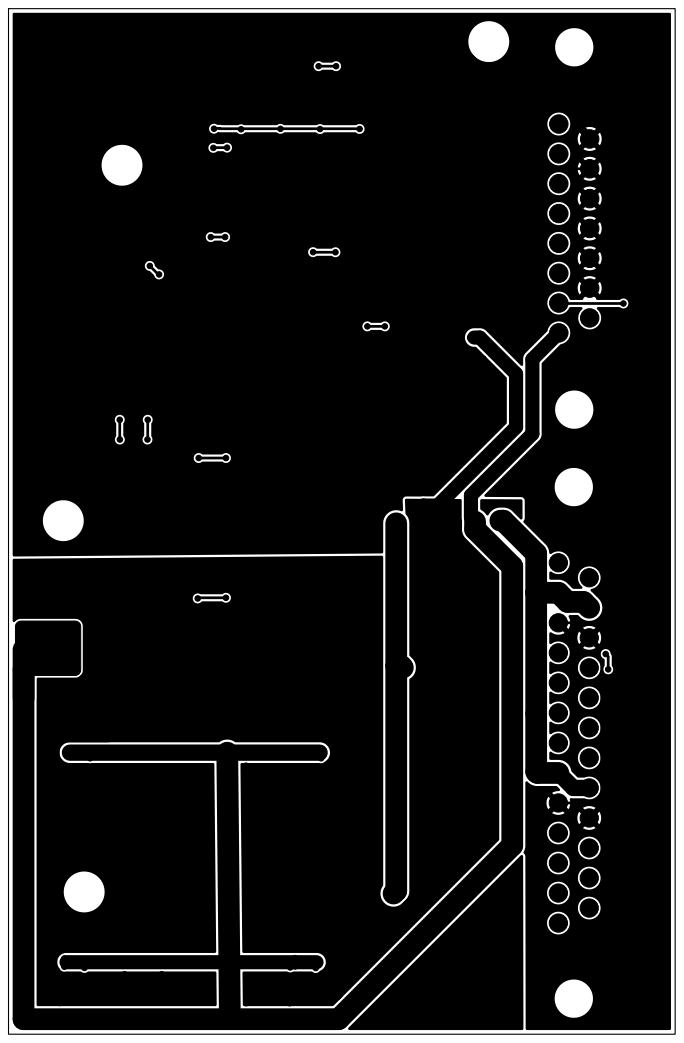
[picture p37: page 1]
