CamMorelli/hshs-project-FirstStageTest/Hardware/HSHS Interface Board 0110B/Assembly Documents/HSHS Interface Board 0110B-F_Cu.pdf

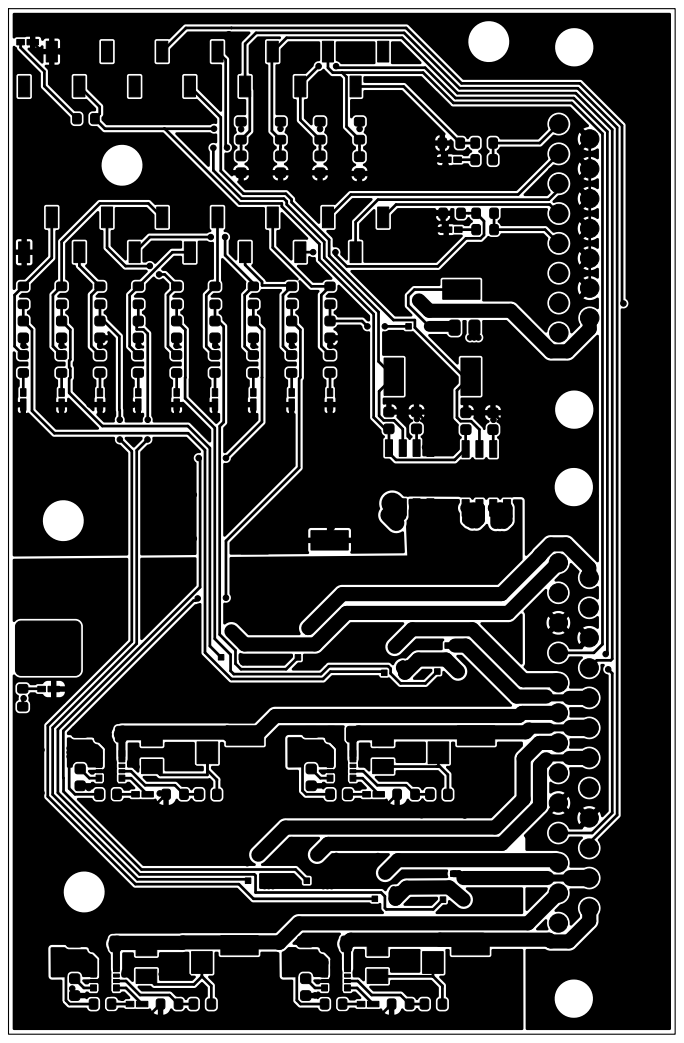
[picture p38: page 1]
