CamMorelli/hshs-project-FirstStageTest/Hardware/HSHS Interface Board 0110B/Assembly Documents/HSHS Interface Board 0110B-F_Fab.pdf

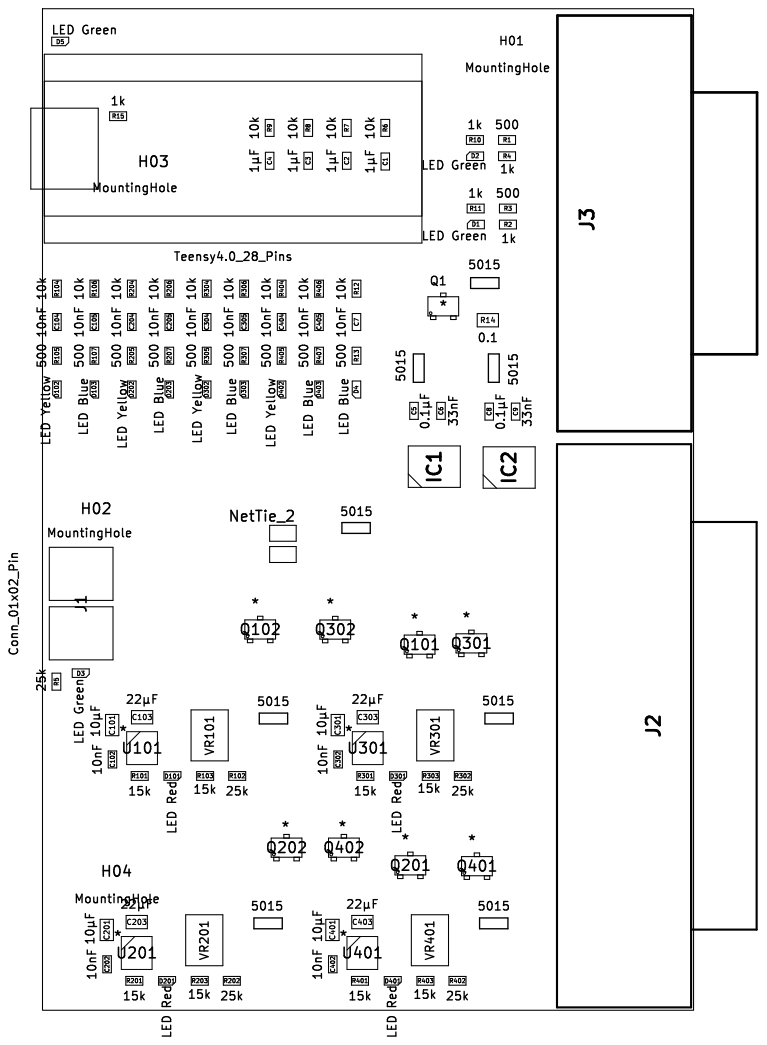
[picture p39: page 1]
