CamMorelli/hshs-project-FirstStageTest/Hardware/HSHS Interface Board 0110B/Assembly Documents/HSHS Interface Board 0110B-F_Mask.pdf

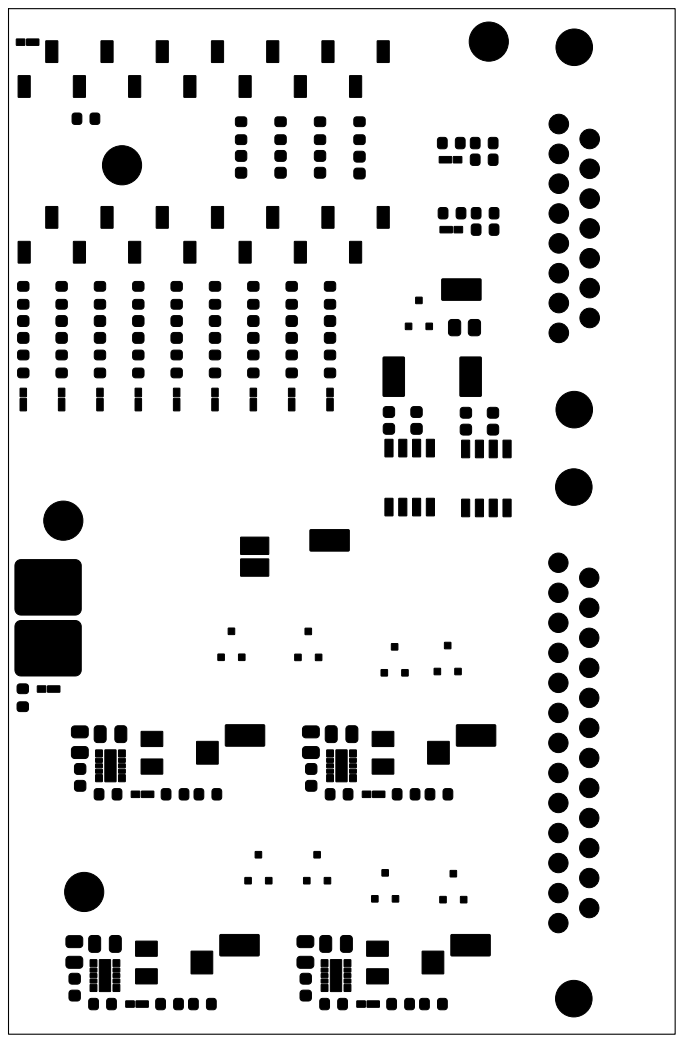
[picture p40: page 1]
