CamMorelli/hshs-project-FirstStageTest/Hardware/HSHS Interface Board 1010C/Assembly Documents/HSHS Interface Board 1010C-B_Cu.pdf

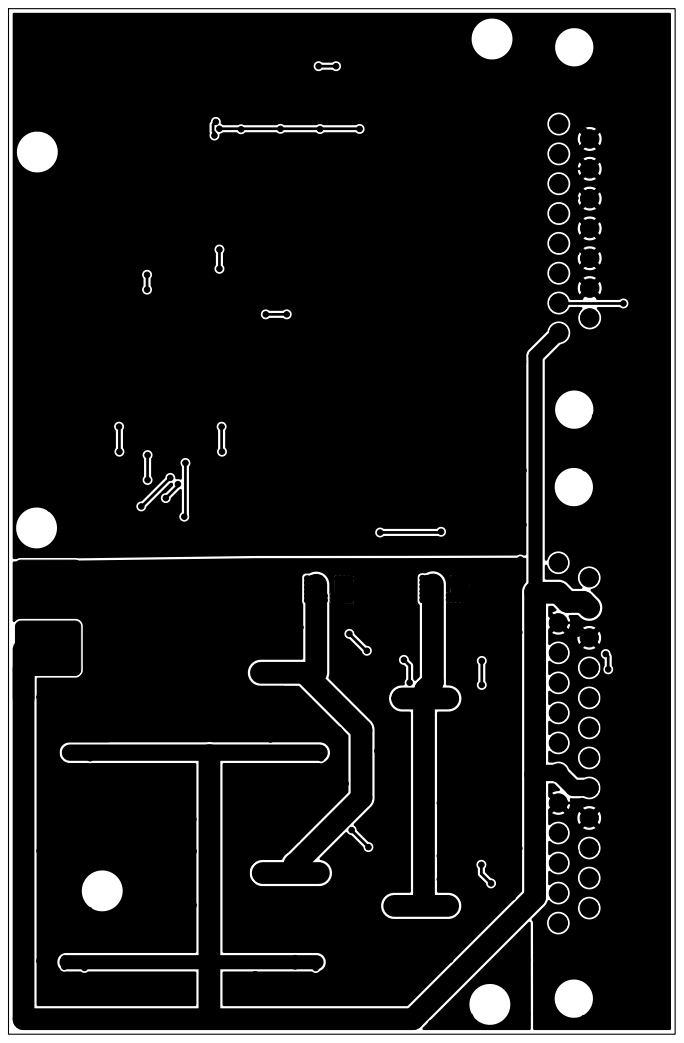
[picture p43: page 1]
