CamMorelli/hshs-project-FirstStageTest/Hardware/HSHS Interface Board 1010C/Assembly Documents/HSHS Interface Board 1010C-F_Cu.pdf

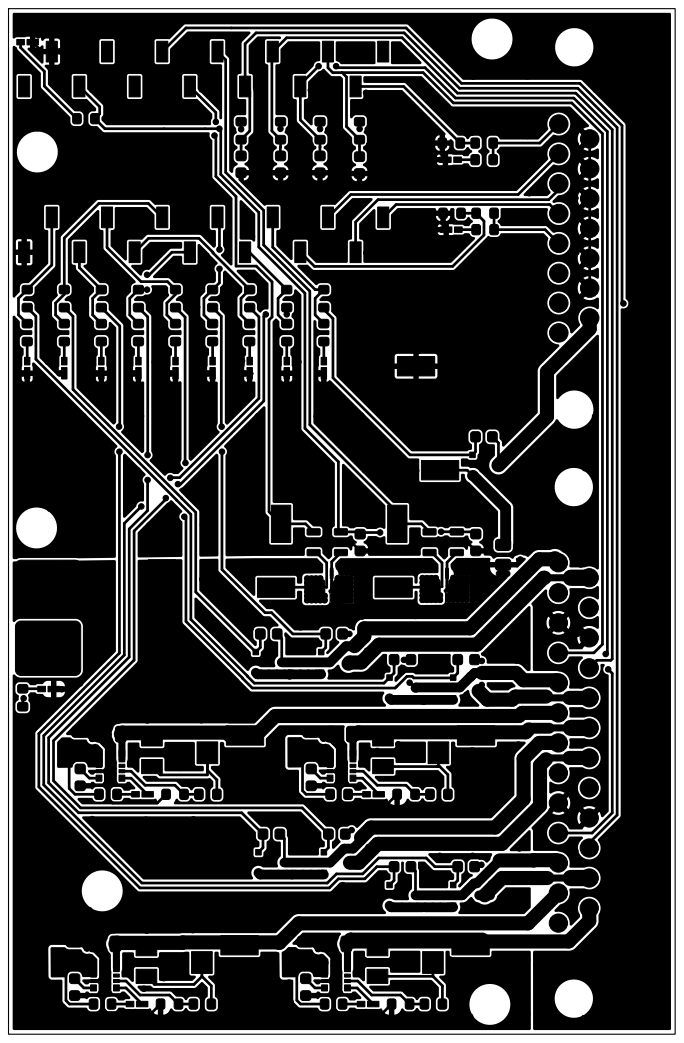
[picture p44: page 1]
