CamMorelli/hshs-project-FirstStageTest/Hardware/HSHS Interface Board 1010C/Assembly Documents/HSHS Interface Board 1010C-F_Mask.pdf

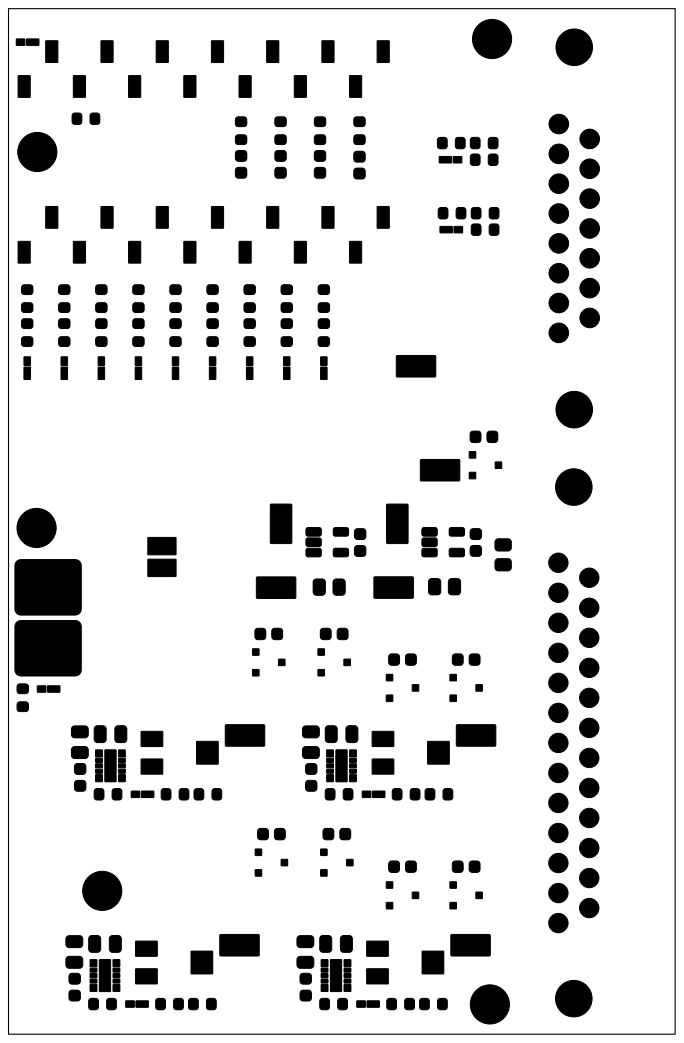
[picture p45: page 1]
