CamMorelli/hshs-project-FirstStageTest/Hardware/HSHS Interface Board/Assembly Documents/Print2.pdf

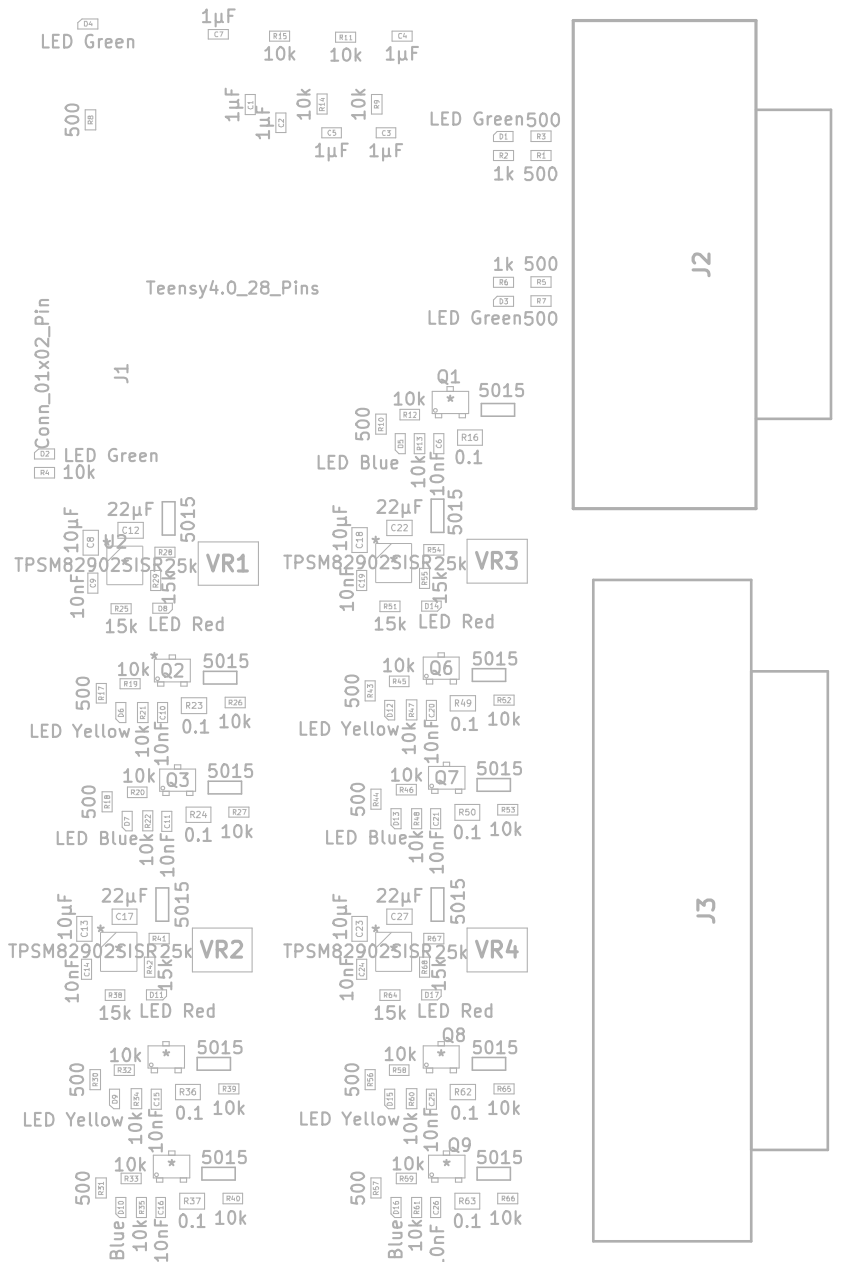
[picture p48: page 1]
