CamMorelli/hshs-project-FirstStageTest/Hardware/HSHS Test Board 0111/Assembly Docs/HSHS Test Board 0111-B_Cu.pdf

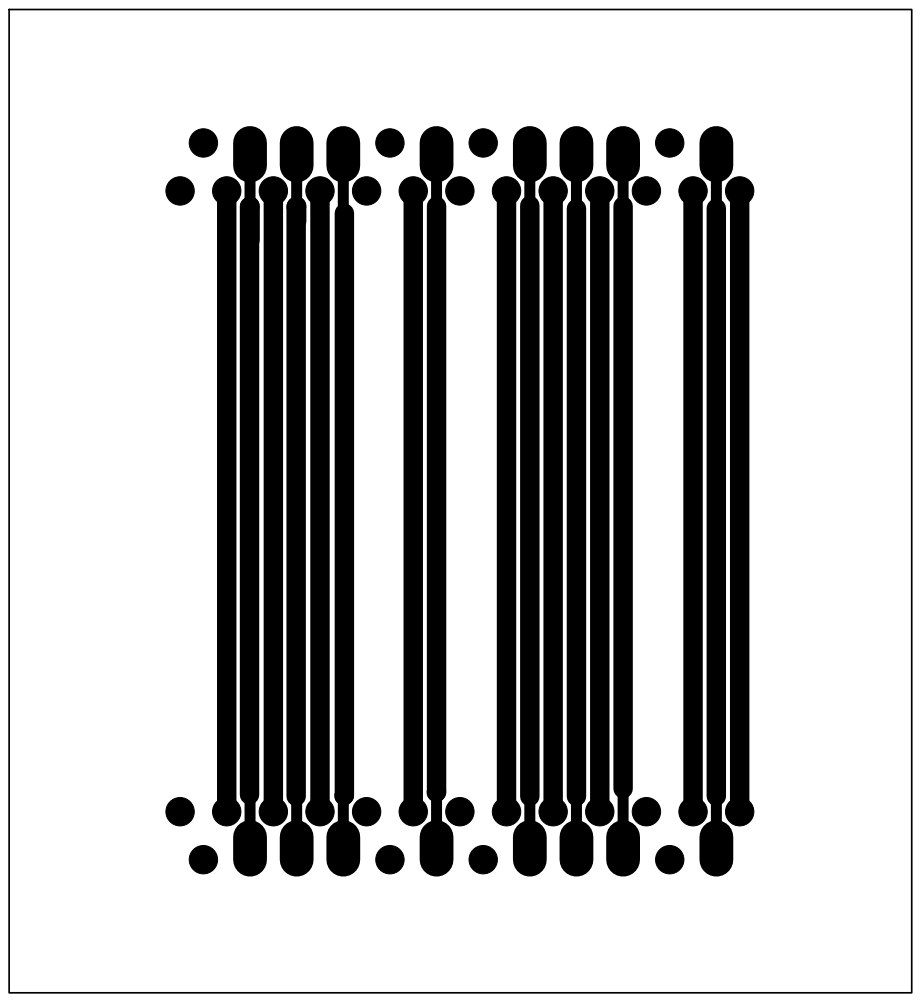
[picture p49: page 1]
