CamMorelli/hshs-project-FirstStageTest/Hardware/HSHS Test Board 0111/Assembly Docs/HSHS Test Board 0111-F_Cu.pdf

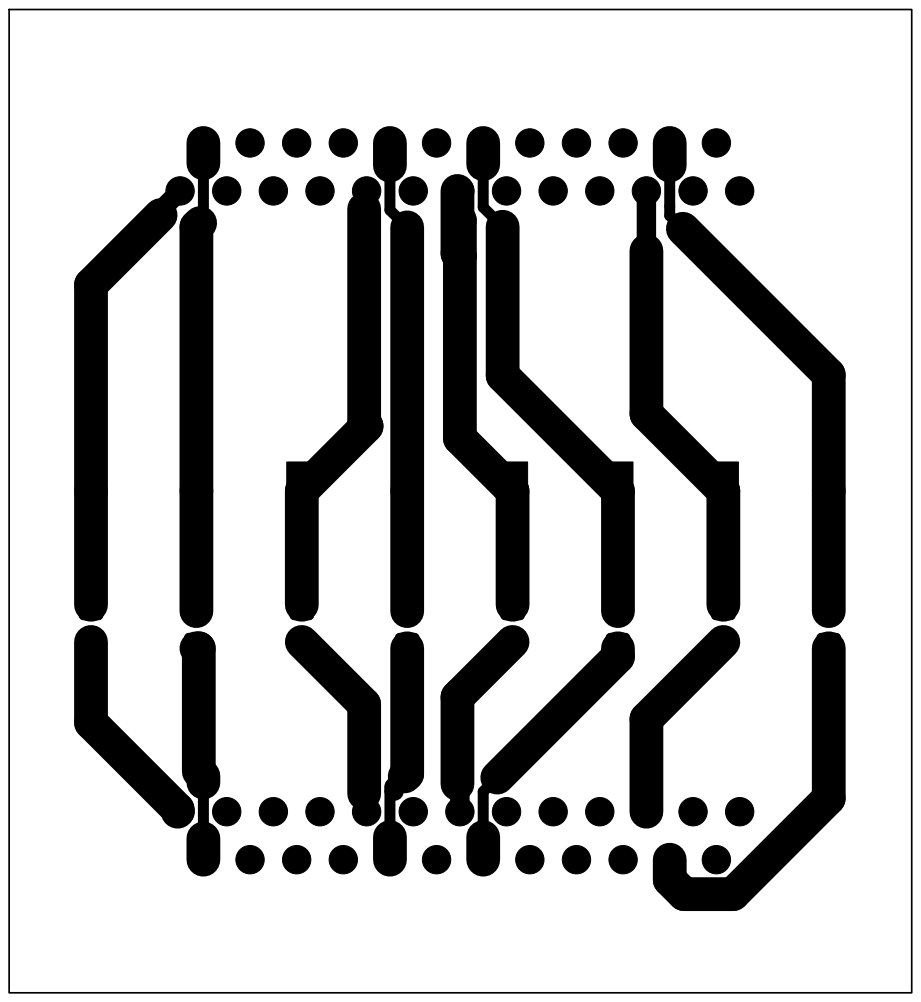
[picture p50: page 1]
