CamMorelli/hshs-project-FirstStageTest/Hardware/HSHS Test Board 0111/Assembly Docs/HSHS Test Board 0111-F_Fab.pdf

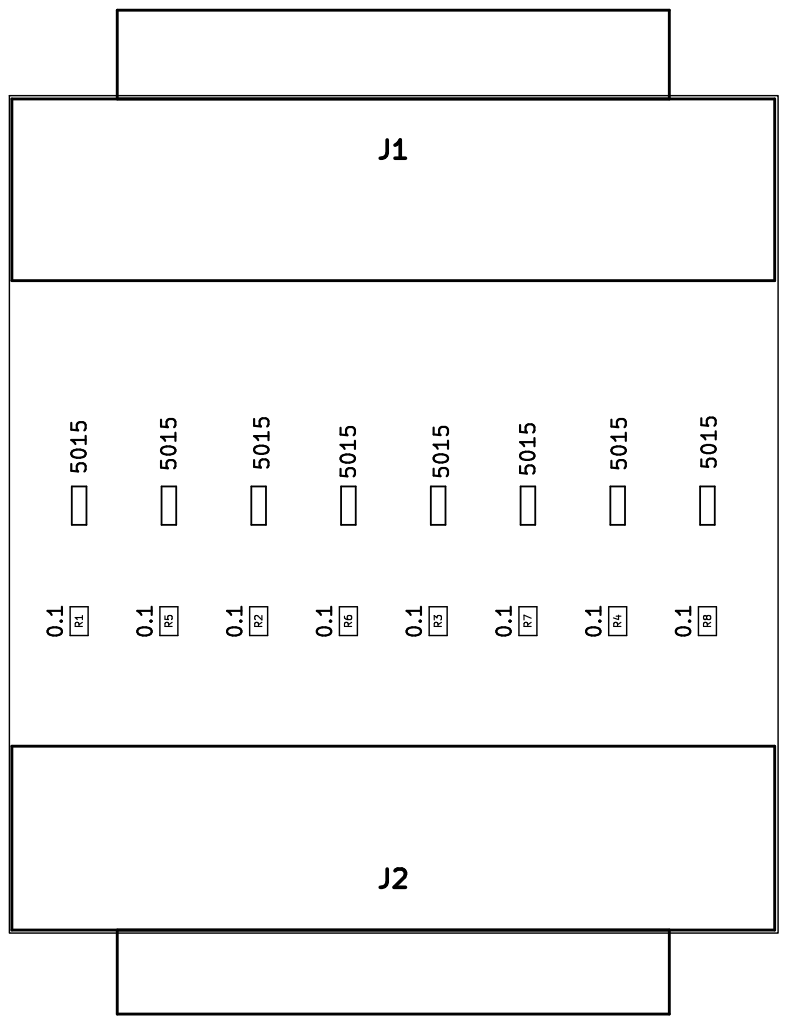
[picture p51: page 1]
