CamMorelli/hshs-project-FirstStageTest/Hardware/HSHS Test Board 0111/docs/Connectors/ENG_CD_5788794_C.pdf

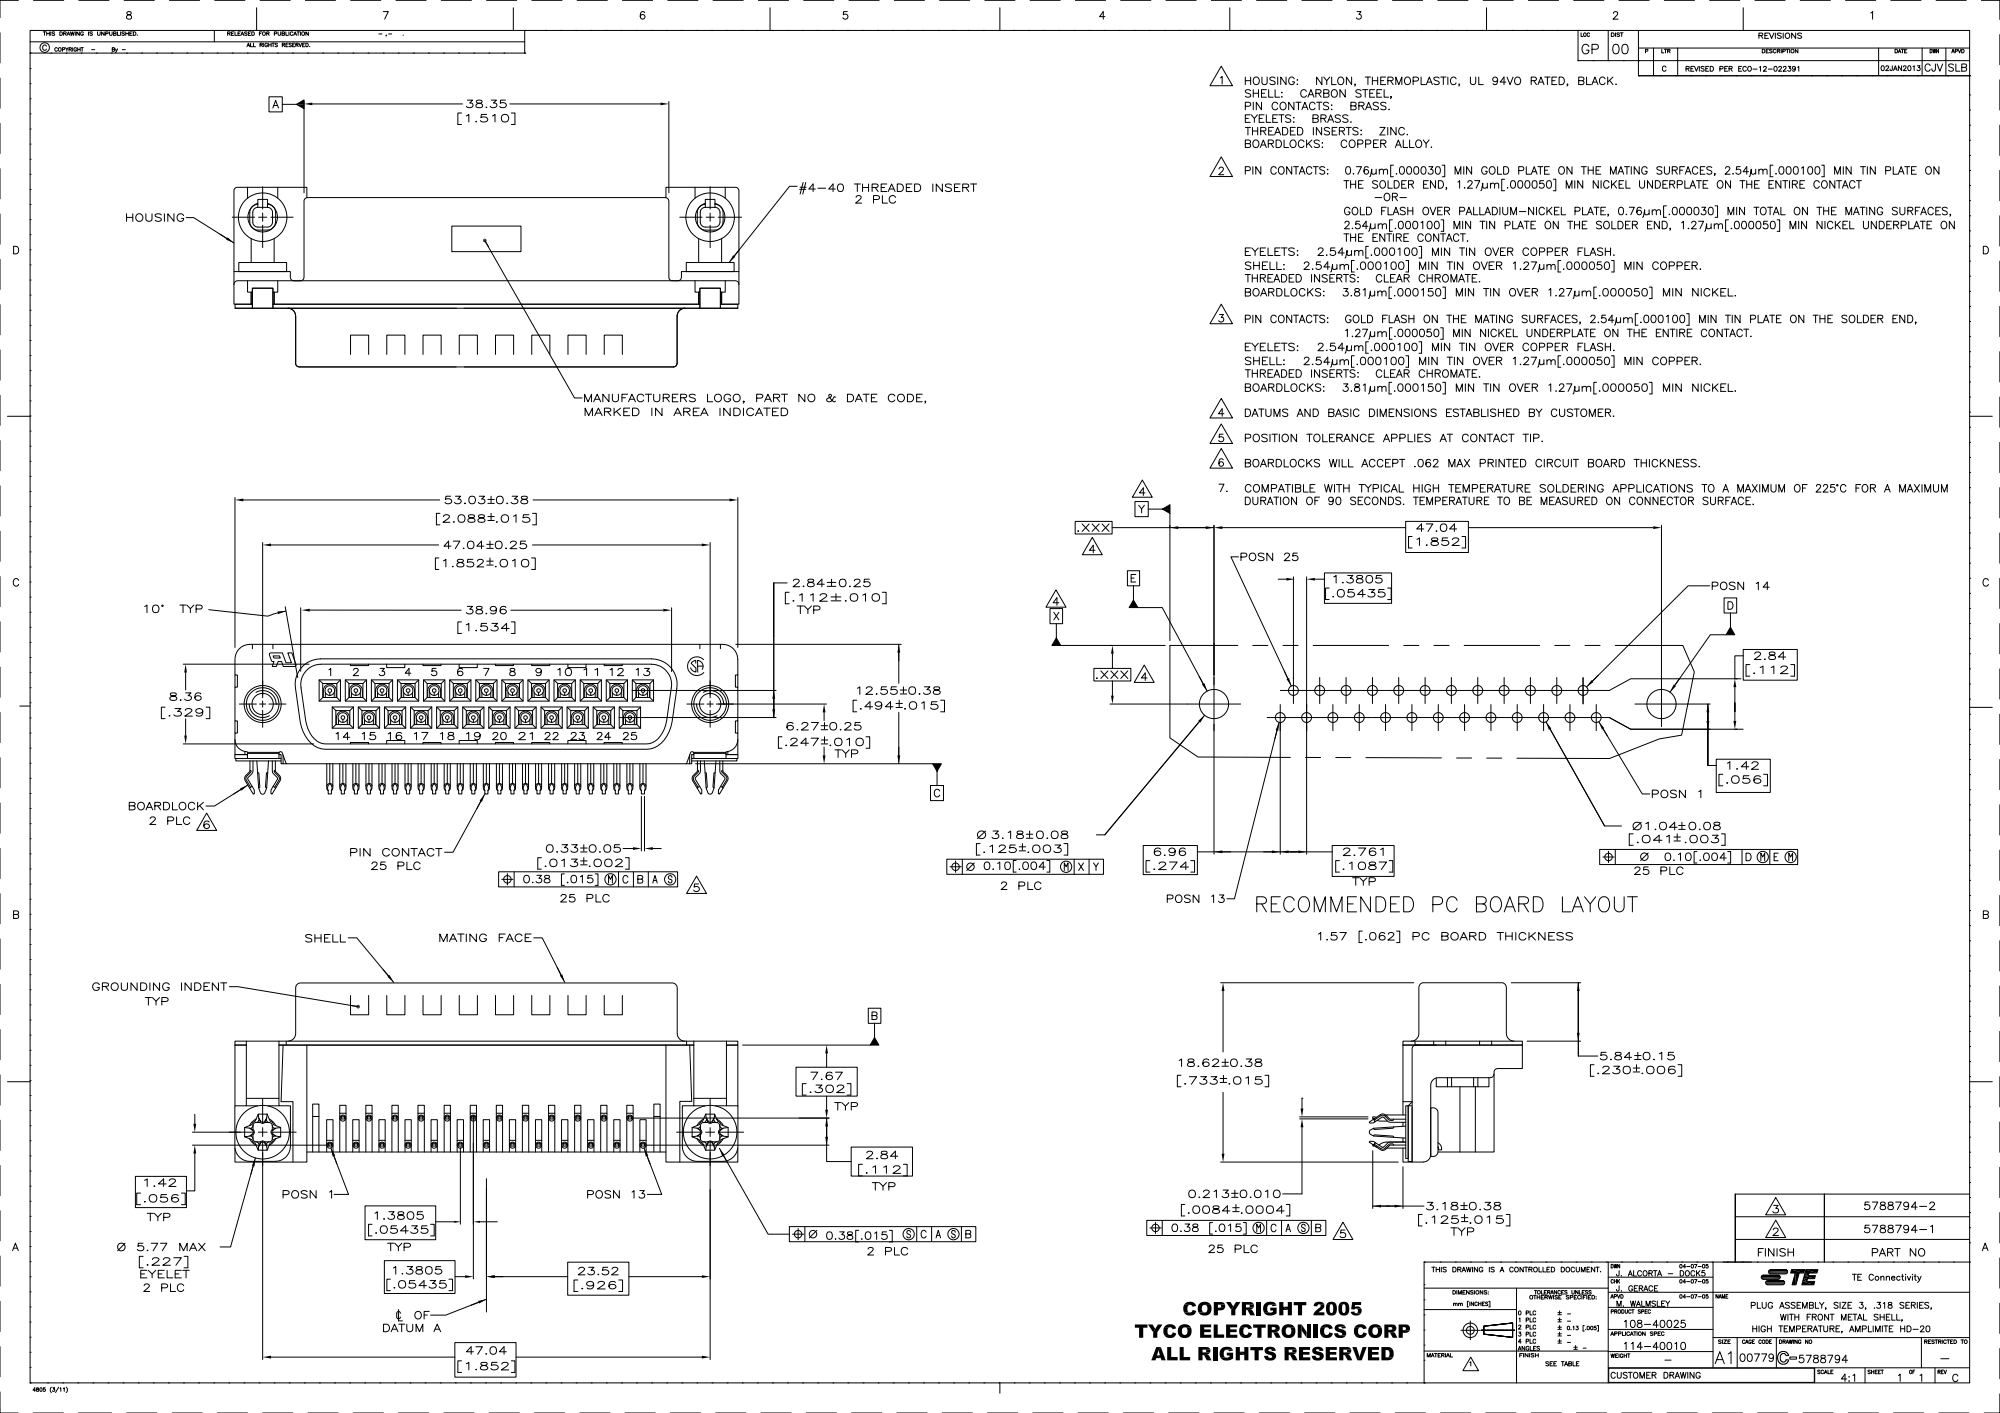
[picture p52: page 1]
