CamMorelli/hshs-project-FirstStageTest/ExampleCode/include/SpinGenApi/Pointer.h

//=============================================================================
// Copyright (c) 2001-2021 FLIR Systems, Inc. All Rights Reserved.
//
// This software is the confidential and proprietary information of FLIR
// Integrated Imaging Solutions, Inc. ("Confidential Information"). You
// shall not disclose such Confidential Information and shall use it only in
// accordance with the terms of the license agreement you entered into
// with FLIR Integrated Imaging Solutions, Inc. (FLIR).
//
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
#ifndef SPINNAKER_GENAPI_POINTER_H
#define SPINNAKER_GENAPI_POINTER_H

#include "Base.h"
#include "INode.h"
#include "IValue.h"
#include "ICategory.h"
#include "IInteger.h"
#include "IFloat.h"
#include "IRegister.h"
#include "IEnumeration.h"
#include "IEnumEntry.h"
#include "IBoolean.h"
#include "IPort.h"
#include "IPortRecorder.h"
#include "IPortConstruct.h"
#include "IChunkPort.h"
#include "IString.h"
#include "INodeMap.h"
#include "INodeMapDyn.h"
#include "IDestroy.h"
#include "IDeviceInfo.h"
#include "ISelector.h"
#include "ICommand.h"
#include "GCString.h"
#include "../Exception.h"
#include <stdio.h>

// Windows-specific.
#if defined(WIN32) || defined(_WIN32) || defined(WIN64) || defined(_WIN64)
// Linux specific.
#else
// End of OS-specific code.
#endif

namespace Spinnaker
{
    namespace GenApi
    {
        /**
         *  @defgroup SpinnakerGenApiClasses Spinnaker GenApi Classes
         */
        /*@{*/

        /**
         *  @defgroup Pointer_h Pointer Class
         */
        /*@{*/

        //*************************************************************
        // CPointer class
        //*************************************************************

        /**
         * @brief Encapsulates a GenApi pointer dealing with the dynamic_cast automatically
         */
        template <class T, class B = IBase> class CPointer
        {

          public:
            /**
             * Default constructor.
             */
            CPointer(void) : m_pT(NULL)
            {
            }
            /**
             * Constructor from INode pointer type.
             */
            CPointer(B* pB) : m_pT(dynamic_cast<T*>(pB))
            {
            }

            virtual ~CPointer(void)
            {
            }
            /**
             * Assign INode Pointer
             */
            void operator=(B* pB)
            {
                m_pT = dynamic_cast<T*>(pB);
            }
            /**
             * Dereferencing
             */
            operator T*(void)const
            {
                if (nullptr == m_pT)
                {
                    throw Spinnaker::Exception(
                        __LINE__,
                        __FILE__,
                        __FUNCTION__,
                        "LogicalErrorException NULL pointer dereferenced",
                        SPINNAKER_ERR_GENICAM_LOGICAL);
                }
                return m_pT;
            }

            /**
             * Dereferencing
             */
            T& operator*(void)const
            {
                if (nullptr == m_pT)
                {
                    throw Spinnaker::Exception(
                        __LINE__,
                        __FILE__,
                        __FUNCTION__,
                        "LogicalErrorException NULL pointer dereferenced",
                        SPINNAKER_ERR_GENICAM_LOGICAL);
                }
                return *m_pT;
            }

            /**
             * Dereferencing
             */
            T& operator()(void) const
            {
                if (nullptr == m_pT)
                {
                    throw Spinnaker::Exception(
                        __LINE__,
                        __FILE__,
                        __FUNCTION__,
                        "LogicalErrorException NULL pointer dereferenced",
                        SPINNAKER_ERR_GENICAM_LOGICAL);
                }
                return *m_pT;
            }

            /**
             * Dereferencing
             */
            T* operator->(void)const
            {
                if (nullptr == m_pT)
                {
                    throw Spinnaker::Exception(
                        __LINE__,
                        __FILE__,
                        __FUNCTION__,
                        "LogicalErrorException NULL pointer dereferenced",
                        SPINNAKER_ERR_GENICAM_LOGICAL);
                }
                return m_pT;
            }

            /**
             * true if the pointer is valid
             */
            bool IsValid() const throw()
            {
                return m_pT != nullptr;
            }

            /**
             * true if the pointer is valid
             */
            operator bool(void) const throw()
            {
                return m_pT != nullptr;
            }

            /**
             * pointer equal
             */
            bool operator==(T* pT) const
            {
                return m_pT == pT;
            }

            /**
             * pointer equal
             */
            bool operator==(const CPointer<T, B>& rT) const
            {
                return m_pT == rT.m_pT;
            }

            /**
             * pointer equal
             */
            bool operator==(int nMustBeNull) const
            {
                if (0 != nMustBeNull)
                {
                    throw Spinnaker::Exception(
                        __LINE__,
                        __FILE__,
                        __FUNCTION__,
                        "LogicalErrorException argument must be NULL",
                        SPINNAKER_ERR_GENICAM_LOGICAL);
                }
                return NULL == m_pT;
            }

            /**
             * pointer inequal
             */
            bool operator!=(const CPointer<T, B>& rT) const
            {
                return m_pT != rT.m_pT;
            }

            /**
             * pointer inequal
             */
            bool operator!=(T* pT) const
            {
                return m_pT != pT;
            }

            /**
             * pointer inequal
             */
            bool operator!=(const long int nMustBeNull) const
            {
                if (0 != nMustBeNull)
                {
                    throw Spinnaker::Exception(
                        __LINE__,
                        __FILE__,
                        __FUNCTION__,
                        "LogicalErrorException argument must be NULL",
                        SPINNAKER_ERR_GENICAM_LOGICAL);
                }
                return NULL != m_pT;
            }

            /**
             * pointer inequal
             */
            bool operator!=(const int nMustBeNull) const
            {
                if (0 != nMustBeNull)
                {
                    throw Spinnaker::Exception(
                        __LINE__,
                        __FILE__,
                        __FUNCTION__,
                        "LogicalErrorException argument must be NULL",
                        SPINNAKER_ERR_GENICAM_LOGICAL);
                }
                return NULL != m_pT;
            }

            /**
             * pointer inequal
             */
            bool operator!=(const std::nullptr_t nullPtr) const
            {
                if (nullPtr != nullptr)
                {
                    throw Spinnaker::Exception(
                        __LINE__,
                        __FILE__,
                        __FUNCTION__,
                        "LogicalErrorException argument must be nullptr",
                        SPINNAKER_ERR_GENICAM_LOGICAL);
                }
                return m_pT != nullptr;
            }

          protected:
            /**
             * Underlying raw pointer.
             */
            T* m_pT;
        };

        /*@}*/
        /*@}*/

        //*************************************************************
        // Smartpointer for all interface
        //*************************************************************

        /**
         * \addtogroup Pointer_h Pointer Class
         * \{
         */

        /**
         * SmartPointer for IBase interface pointer
         */
        typedef CPointer<IBase> CBasePtr;

        /**
         * SmartPointer for INode interface pointer
         */
        typedef CPointer<INode, IBase> CNodePtr;

        /**
         * SmartPointer for IValue interface pointer
         */
        typedef CPointer<IValue> CValuePtr;

        /**
         * SmartPointer for ICategory interface pointer
         */
        typedef CPointer<ICategory> CCategoryPtr;

        /**
         * SmartPointer for IBoolean interface pointer
         */
        typedef CPointer<IBoolean> CBooleanPtr;

        /**
         * SmartPointer for IInteger interface pointer
         */
        typedef CPointer<IInteger> CIntegerPtr;

        /**
         * SmartPointer for IString interface pointer
         */
        typedef CPointer<IString> CStringPtr;

        /**
         * SmartPointer for IRegister interface pointer
         */
        typedef CPointer<IRegister> CRegisterPtr;

        /**
         * SmartPointer for IEnumeration interface pointer
         */
        typedef CPointer<IEnumeration> CEnumerationPtr;

        /**
         * SmartPointer for IEnumEntry interface pointer
         */
        typedef CPointer<IEnumEntry> CEnumEntryPtr;

        /**
         * SmartPointer for IPort interface pointer
         */
        typedef CPointer<IPort> CPortPtr;

        /**
         * SmartPointer for IPortReplay interface pointer
         */
        typedef CPointer<IPortReplay> CPortReplayPtr;

        /**
         * SmartPointer for IPortRecorder interface pointer
         */
        typedef CPointer<IPortRecorder> CPortRecorderPtr;

        /**
         * SmartPointer for IPortWriteList interface pointer
         */
        typedef CPointer<IPortWriteList, IPortWriteList> CPortWriteListPtr;

        /**
         * SmartPointer for IChunkPort interface pointer
         */
        typedef CPointer<IChunkPort> CChunkPortPtr;

        /**
         * SmartPointer for INodeMap interface pointer
         */
        typedef CPointer<INodeMap, INodeMap> CNodeMapPtr;

        /**
         * SmartPointer for INodeMapDyn interface pointer
         */
        typedef CPointer<INodeMapDyn, INodeMap> CNodeMapDynPtr;

        /**
         * SmartPointer for IDeviceInfo interface pointer
         */
        typedef CPointer<IDeviceInfo, INodeMap> CDeviceInfoPtr;

        /**
         * SmartPointer for ISelector interface pointer
         */
        typedef CPointer<ISelector> CSelectorPtr;

        /**
         * SmartPointer for ICommand interface pointer
         */
        typedef CPointer<ICommand> CCommandPtr;

        /**
         * SmartPointer for IPortConstruct interface pointer
         */
        typedef CPointer<IPortConstruct> CPortConstructPtr;

        /**
         *  @addtogroup SpinnakerGenApiClasses Spinnaker GenApi Classes
         */
        /*@{*/

        /**
         *  @addtogroup Pointer_h Pointer Class
         */
        /*@{*/

        /**
         * SmartPointer for IFloat interface pointer
         */
#ifdef SWIG
        %template(_SWIG_CFltPtr)CPointer<IFloat, IBase>; // definition for Python wrapper generation
#endif
        class CFloatPtr : public CPointer<IFloat, IBase>
        {
          public:
            /**
             * Default constructor.
             */
            CFloatPtr() throw() : CPointer<IFloat, IBase>()
            {
            }

            /**
             * Constructor from IBase pointer type.
             */
            CFloatPtr(IBase* pB) : CPointer<IFloat, IBase>(pB)
            {
            }

            /**
             * Assign IBase Pointer
             */
            void operator=(IBase* pB)
            {
                CPointer<IFloat, IBase>::operator=(pB);
            }

            /**
             * gets the interface of an integer alias node.
             */
            IInteger* GetIntAlias()
            {
                return dynamic_cast<IInteger*>(m_pT->GetNode()->GetCastAlias());
            }

            /**
             * gets the interface of an enum alias node.
             */
            IEnumeration* GetEnumAlias()
            {
                return dynamic_cast<IEnumeration*>(m_pT->GetNode()->GetCastAlias());
            }
        };

        /*@}*/
        /*@}*/

        /**
         * \}
         */

        /**
         * \addtogroup Pointer_h Pointer Class
         * \{
         */

        /**
         * Checks if a node is readable
         */
        template <class T, class B> inline bool IsReadable(const Spinnaker::GenApi::CPointer<T, B>& ptr)
        {
            return ptr.IsValid() && IsReadable(ptr->GetAccessMode());
        }

        /**
         * Checks if a node is Writable
         */
        template <class T, class B> inline bool IsWritable(const Spinnaker::GenApi::CPointer<T, B>& ptr)
        {
            return ptr.IsValid() && IsWritable(ptr->GetAccessMode());
        }

        /**
         * Checks if a node is Implemented
         */
        template <class T, class B> inline bool IsImplemented(const Spinnaker::GenApi::CPointer<T, B>& ptr)
        {
            return ptr.IsValid() && IsImplemented(ptr->GetAccessMode());
        }

        /**
         * Checks if a node is Available
         */
        template <class T, class B> inline bool IsAvailable(const Spinnaker::GenApi::CPointer<T, B>& ptr)
        {
            return ptr.IsValid() && IsAvailable(ptr->GetAccessMode());
        }
        /**
         * Returns the name of the main interface as string
         * DEPRICATED, use IBase::GetPrincipalInterfaceType() instead
         */
        inline GenICam::gcstring GetInterfaceName(IBase* pBase)
        {
#ifdef _WIN32
#pragma warning(push) // icc -W4 complains: controlling expression is constant
#pragma warning(disable : 279)
            assert(pBase && "don't call this with a NULL pointer");
#pragma warning(pop)
#else
            assert(pBase && "don't call this with a NULL pointer");
#endif
            CNodePtr ptrNode(pBase);
            switch (ptrNode->GetPrincipalInterfaceType())
            {
            case intfIValue:
                return GenICam::gcstring("IValue");
            case intfIInteger:
                return GenICam::gcstring("IInteger");
            case intfIBoolean:
                return GenICam::gcstring("IBoolean");
            case intfICommand:
                return GenICam::gcstring("ICommand");
            case intfIFloat:
                return GenICam::gcstring("IFloat");
            case intfIString:
                return GenICam::gcstring("IString");
            case intfIRegister:
                return GenICam::gcstring("IRegister");
            case intfICategory:
                return GenICam::gcstring("ICategory");
            case intfIEnumeration:
                return GenICam::gcstring("IEnumeration");
            case intfIEnumEntry:
                return GenICam::gcstring("IEnumEntry");
            case intfIPort:
                return GenICam::gcstring("IPort");
            case intfIBase:
            default:
                return GenICam::gcstring("IBase");
            }
        }

        /**
         * \}
         */
    } // namespace GenApi
} // namespace Spinnaker

#endif // ifndef SPINNAKER_GENAPI_POINTER_H
